Matthew0826/NULunabotics/Mechanical/Chassis/Chassis v4/1602-0032-0008 assembly.STEP

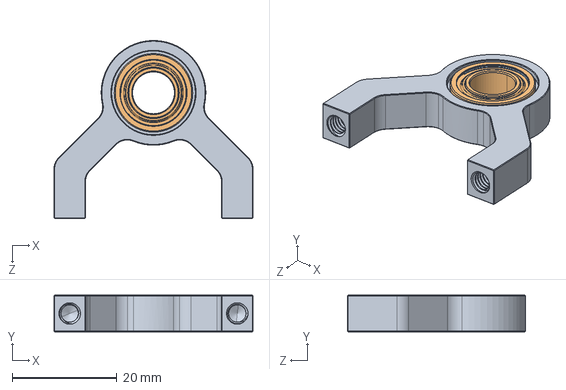
[picture p1: CAD file, 2025-11-15]
Mechanical/Chassis/Chassis v4/1602-0032-0008 assembly.STEP
38.0 x 7.00 x 34.0 mm
