Matthew0826/NULunabotics/Electrical/SparkMiniMount.SLDPRT

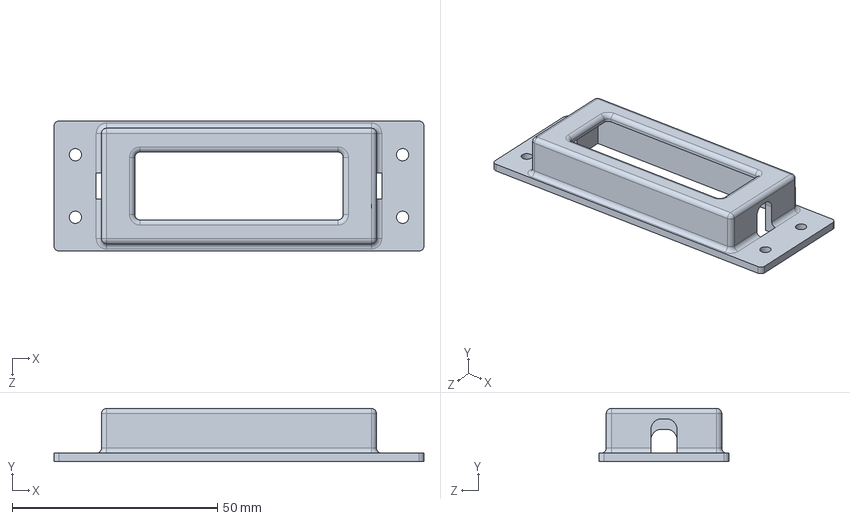
[picture p2: CAD file, 2025-05-19]
Electrical/SparkMiniMount.SLDPRT
90.2 x 13.0 x 31.8 mm
