Matthew0826/NULunabotics/Mechanical/4BarGBOuter.STL

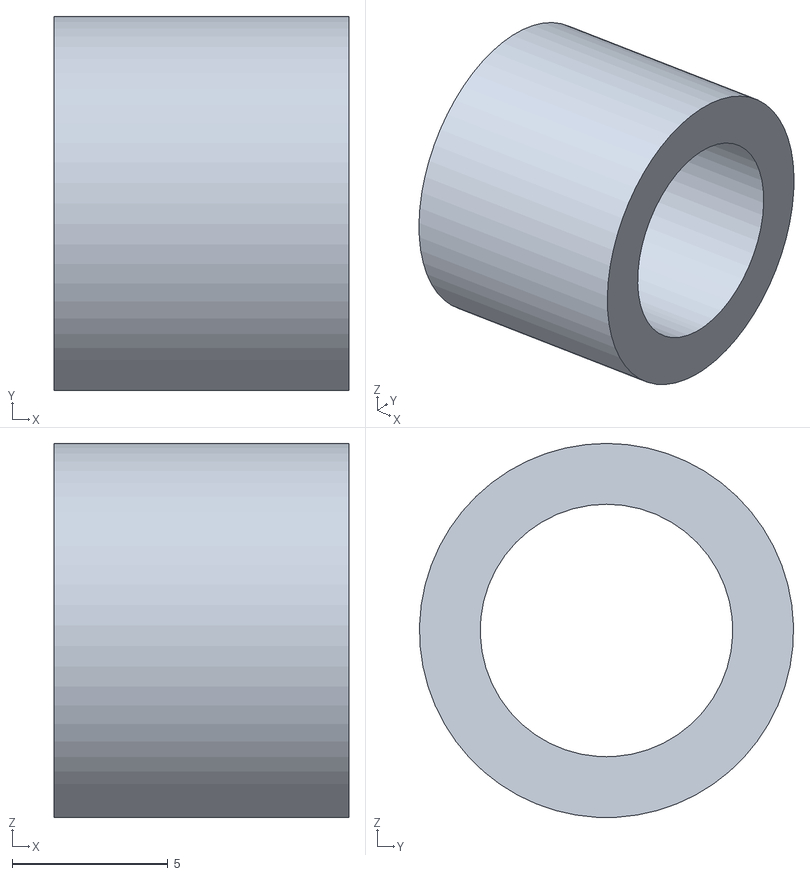
[picture p3: CAD file, 2025-11-15]
Mechanical/4BarGBOuter.STL
9.46 x 12.0 x 12.0
