Matthew0826/NULunabotics/Mechanical/Chassis/Chassis v4/LargeBottomPlate.SLDPRT

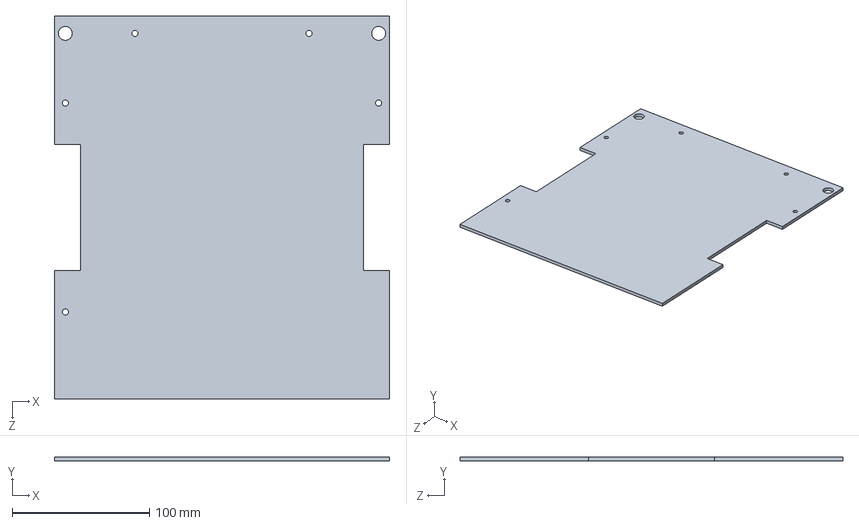
[picture p4: CAD file, 2025-11-15]
Mechanical/Chassis/Chassis v4/LargeBottomPlate.SLDPRT
244.5 x 3.17 x 279.4 mm
