Matthew0826/NULunabotics/Mechanical/Chassis/Maharshi Blocking/Dummy_Wheel_226mm.SLDPRT

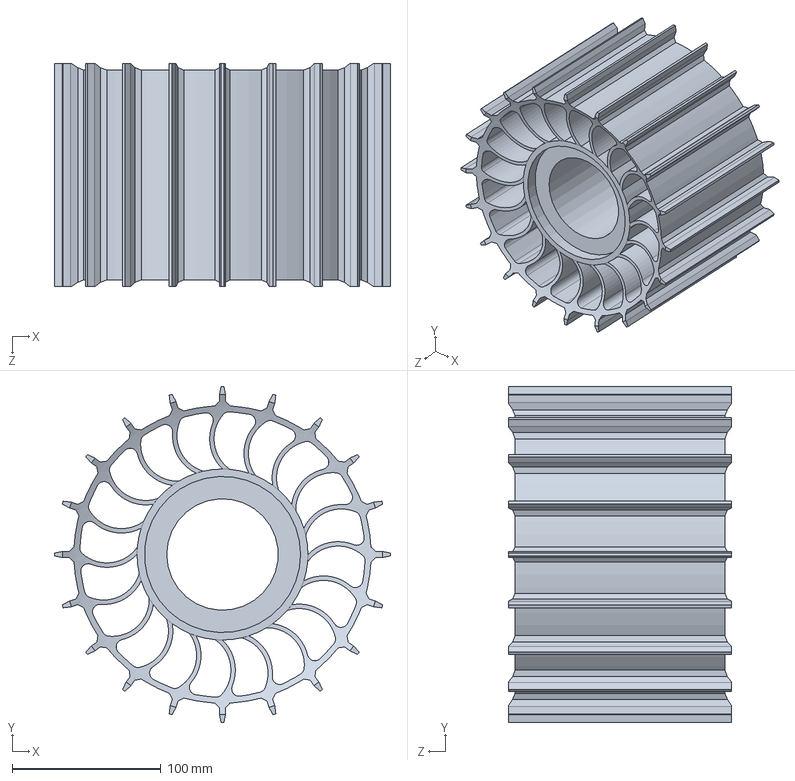
[picture p5: CAD file, 2025-02-20]
Mechanical/Chassis/Maharshi Blocking/Dummy_Wheel_226mm.SLDPRT
226.0 x 226.0 x 150.0 mm
