Matthew0826/NULunabotics/Mechanical/Drivebase/Chassis/Bearing Holder Standard.SLDPRT

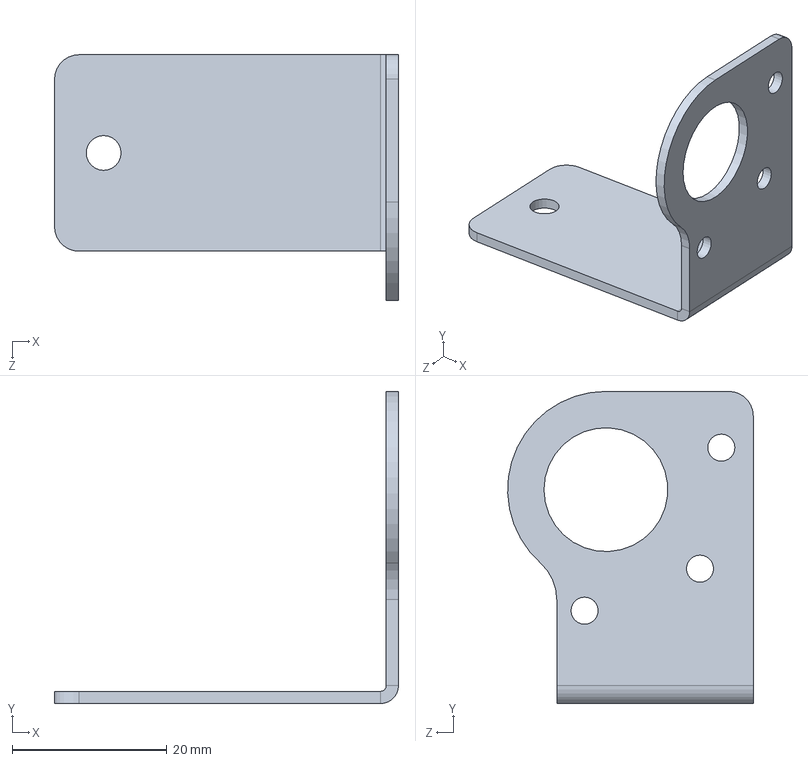
[picture p6: CAD file, 2025-11-15]
Mechanical/Drivebase/Chassis/Bearing Holder Standard.SLDPRT
44.5 x 40.3 x 31.7 mm
