Matthew0826/NULunabotics/Mechanical/Drivebase/Chassis/Frame/Side L-Bar.SLDPRT

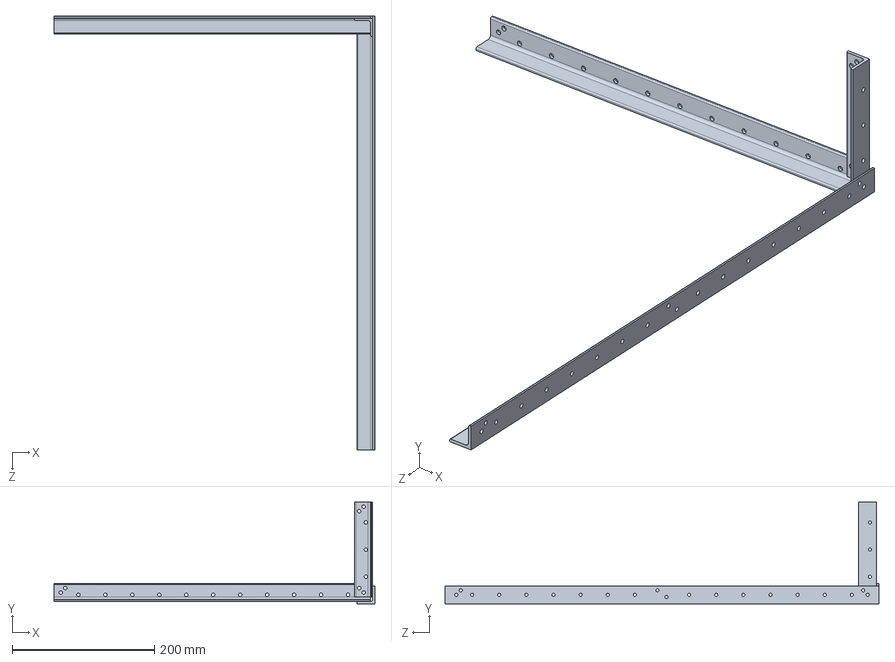
[picture p7: CAD file, 2025-11-15]
Mechanical/Drivebase/Chassis/Frame/Side L-Bar.SLDPRT
450.8 x 142.9 x 609.6 mm
