Matthew0826/NULunabotics/Mechanical/Excavation/Conveyer/Excavator Spacer 1.1in.STL

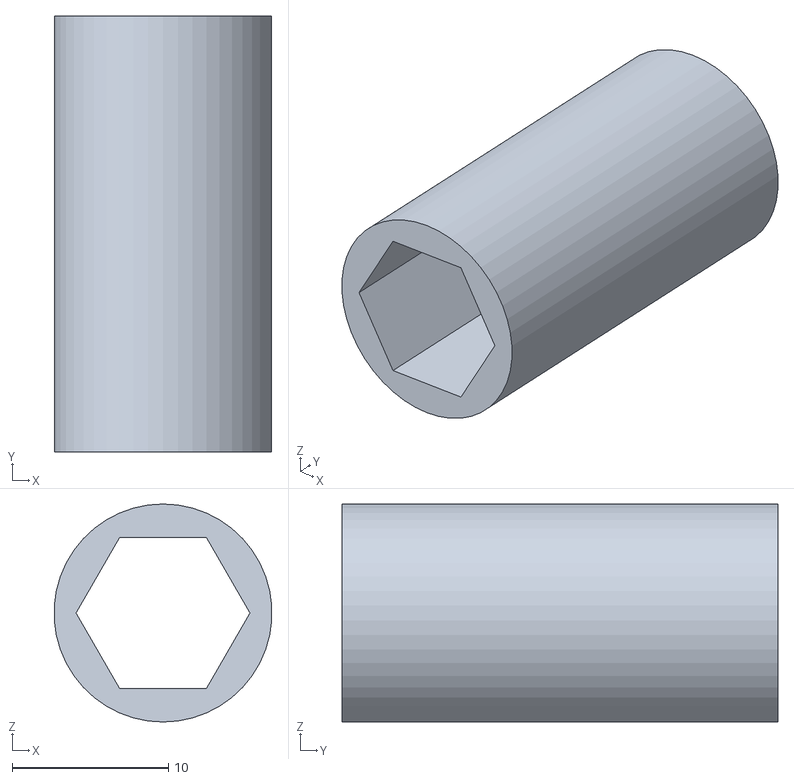
[picture p8: CAD file, 2025-03-28]
Mechanical/Excavation/Conveyer/Excavator Spacer 1.1in.STL
13.9 x 27.9 x 14.0
