Matthew0826/NULunabotics/Mechanical/Excavation/Dump/DumpCut.DXF

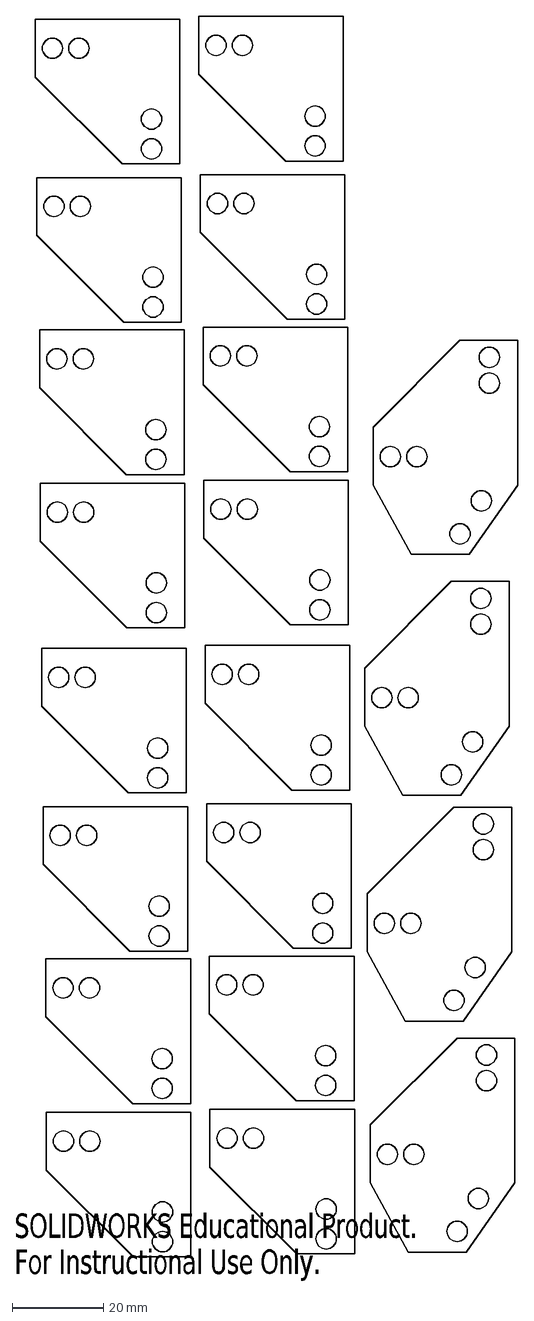
[picture p9: CAD file, 2025-11-15]
Mechanical/Excavation/Dump/DumpCut.DXF
SOLIDWORKS Educational Product.
For Instructional Use Only.
