Matthew0826/NULunabotics/Mechanical/Excavation/Excavator/Waterjet Reference_imported_DWG.dxf

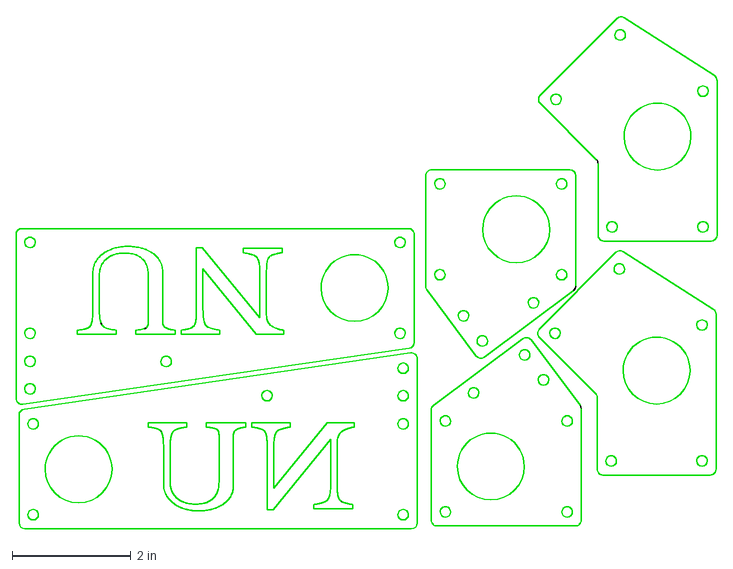
[picture p10: CAD file, 2025-11-15]
Mechanical/Excavation/Excavator/Waterjet Reference_imported_DWG.dxf
11.8 x 8.62 in
