Matthew0826/NULunabotics/Mechanical/Excavation/hexHoldPlate.SLDPRT

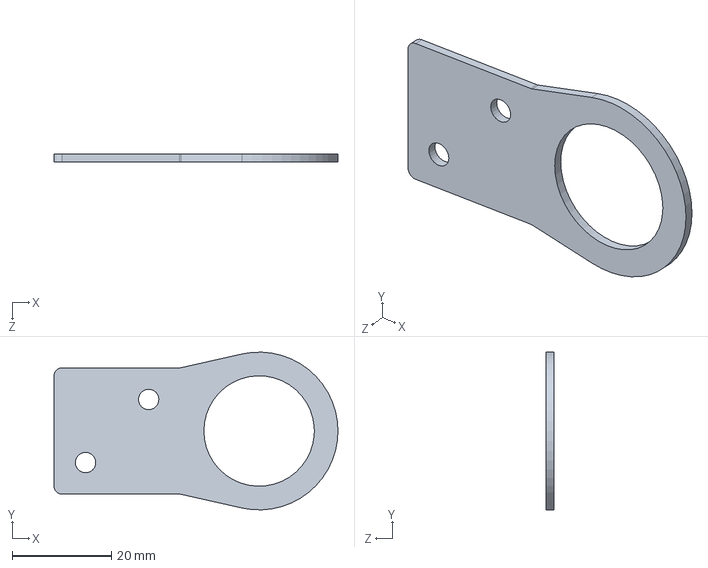
[picture p11: CAD file, 2025-11-15]
Mechanical/Excavation/hexHoldPlate.SLDPRT
57.2 x 31.7 x 1.59 mm
