Matthew0826/NULunabotics/Mechanical/Excavation/Scoops/Excavator Spacer 2.22 in.SLDPRT

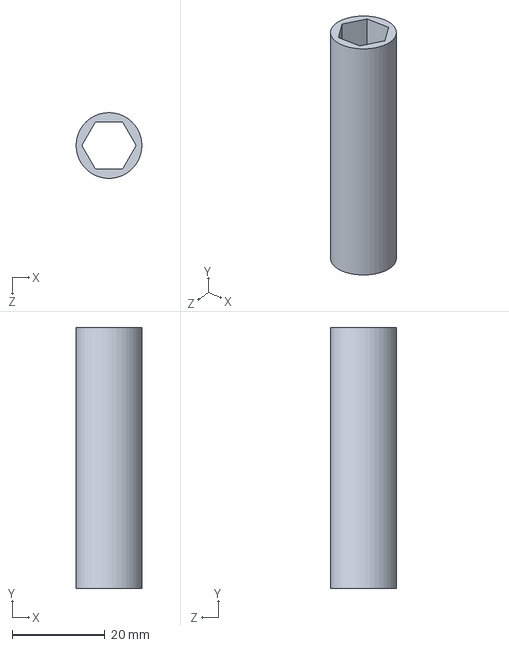
[picture p12: CAD file, 2025-03-31]
Mechanical/Excavation/Scoops/Excavator Spacer 2.22 in.SLDPRT
14.2 x 56.4 x 14.2 mm
