Matthew0826/NULunabotics/Mechanical/Experimental/Swerve Modules/Chassis Structure/Fixed Components/Gearbox Casing/Motor Mounting Plate.SLDPRT

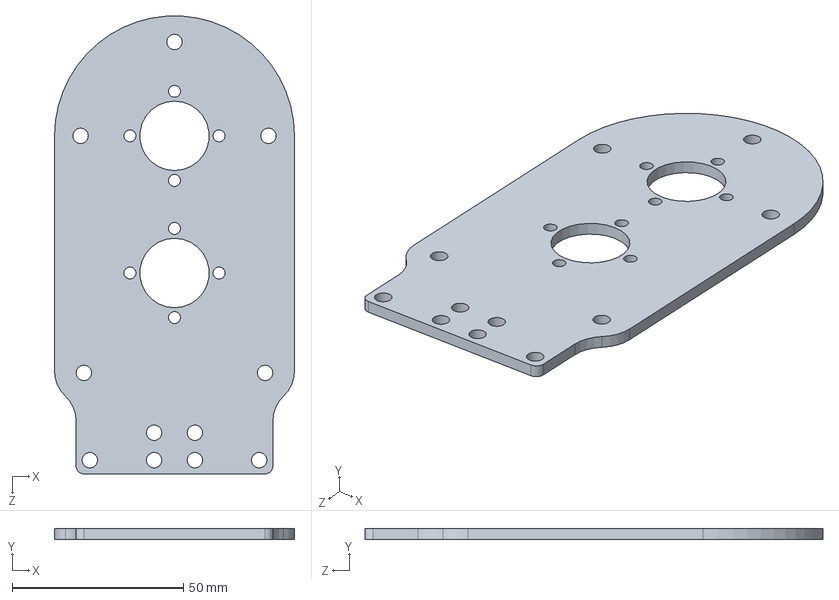
[picture p13: CAD file, 2025-11-15]
Mechanical/Experimental/Swerve Modules/Chassis Structure/Fixed Components/Gearbox Casing/Motor Mounting Plate.SLDPRT
70.0 x 3.18 x 133.5 mm
