Matthew0826/NULunabotics/Mechanical/Experimental/Swerve Modules/Chassis Structure/Fixed Components/Tube Mount/Tube Clamp Plate.SLDPRT

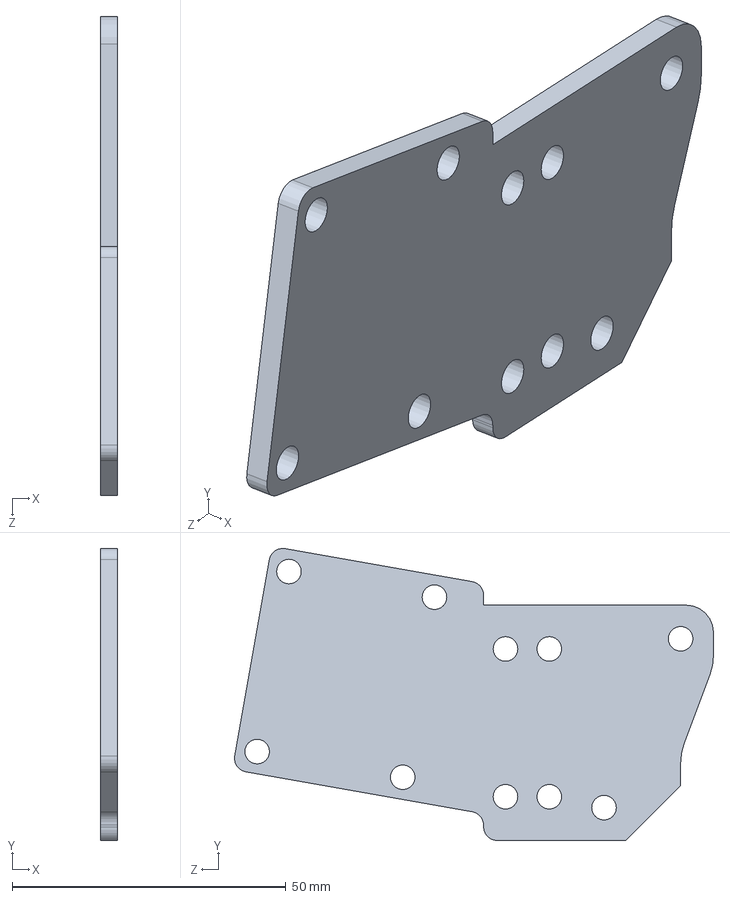
[picture p14: CAD file, 2025-11-15]
Mechanical/Experimental/Swerve Modules/Chassis Structure/Fixed Components/Tube Mount/Tube Clamp Plate.SLDPRT
3.17 x 53.4 x 87.5 mm
