Matthew0826/NULunabotics/Mechanical/Experimental/Swerve Modules/Chassis Structure/Top Spacer.SLDPRT

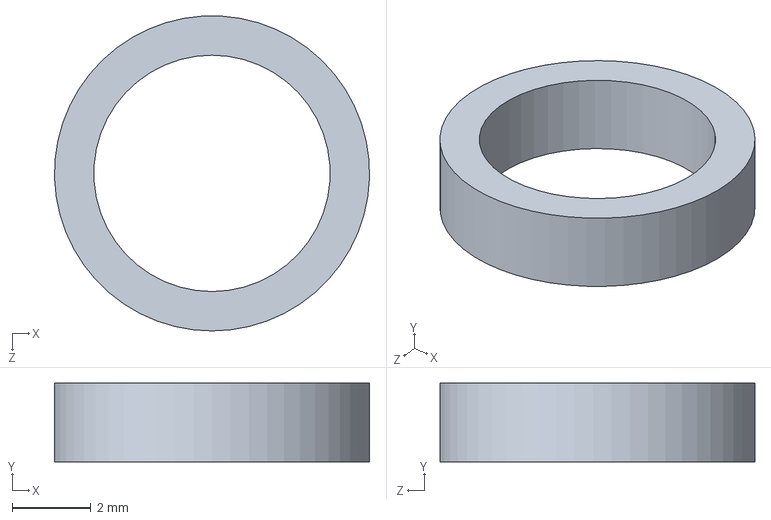
[picture p15: CAD file, 2025-11-15]
Mechanical/Experimental/Swerve Modules/Chassis Structure/Top Spacer.SLDPRT
8.00 x 2.00 x 7.99 mm
