Matthew0826/NULunabotics/Mechanical/Experimental/Swerve Modules/LidarMount.SLDPRT

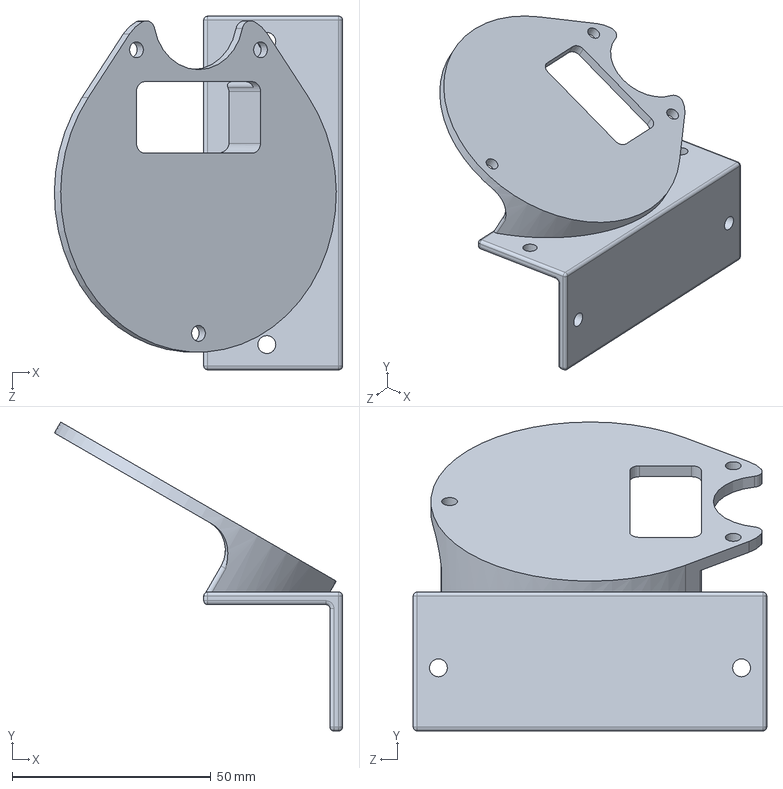
[picture p16: CAD file, 2025-11-15]
Mechanical/Experimental/Swerve Modules/LidarMount.SLDPRT
72.5 x 77.7 x 88.9 mm
