Matthew0826/NULunabotics/Mechanical/Experimental/Swerve Modules/Wheel Structure/Fixed Components/Wheel Tube.SLDPRT

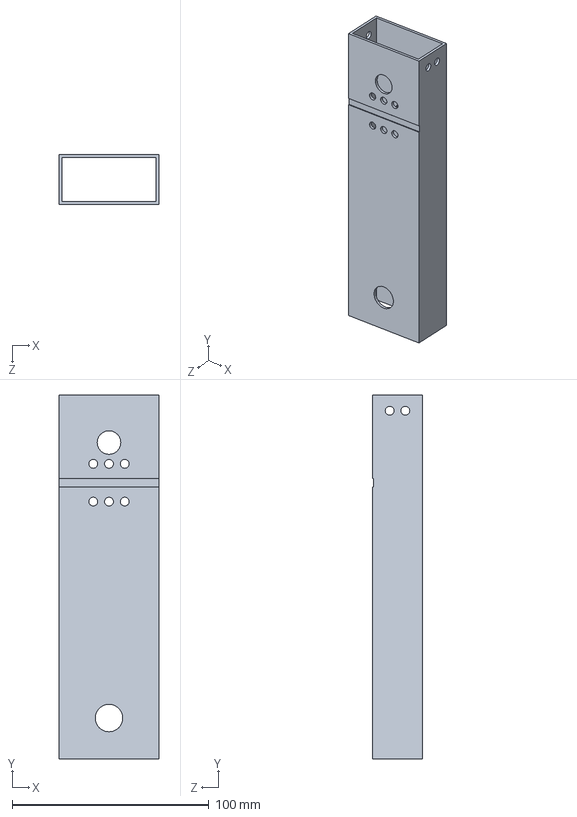
[picture p17: CAD file, 2025-11-15]
Mechanical/Experimental/Swerve Modules/Wheel Structure/Fixed Components/Wheel Tube.SLDPRT
50.8 x 185.0 x 25.4 mm
