Matthew0826/NULunabotics/Mechanical/Experimental/Swerve Modules/Wheel Structure/Grouser Wheel Standin.SLDPRT

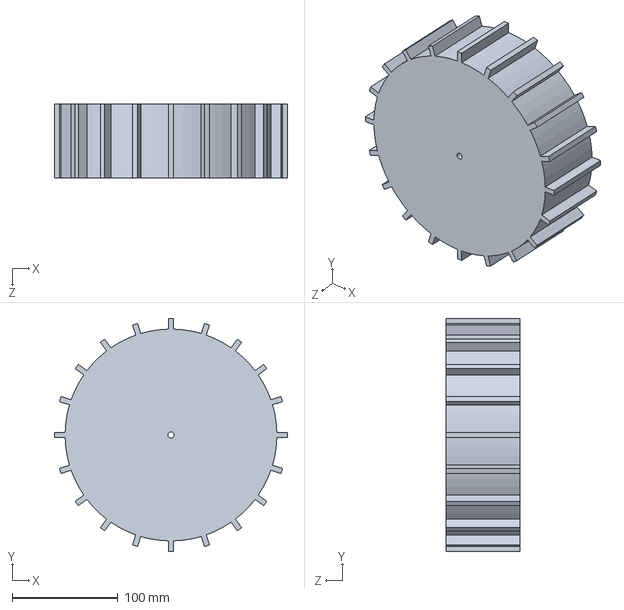
[picture p18: CAD file, 2025-11-15]
Mechanical/Experimental/Swerve Modules/Wheel Structure/Grouser Wheel Standin.SLDPRT
220.0 x 220.0 x 70.0 mm
