Matthew0826/NULunabotics/Mechanical/Generic Parts/Motor.SLDPRT

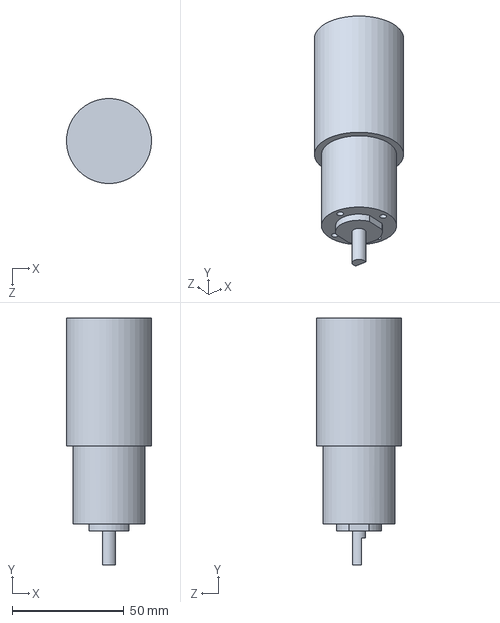
[picture p19: CAD file, 2025-11-15]
Mechanical/Generic Parts/Motor.SLDPRT
38.0 x 110.3 x 38.0 mm
