Matthew0826/NULunabotics/Mechanical/Lunabotics2025_Chassis_Design/Chassis_2/1x1inch_60mmBeam.SLDPRT

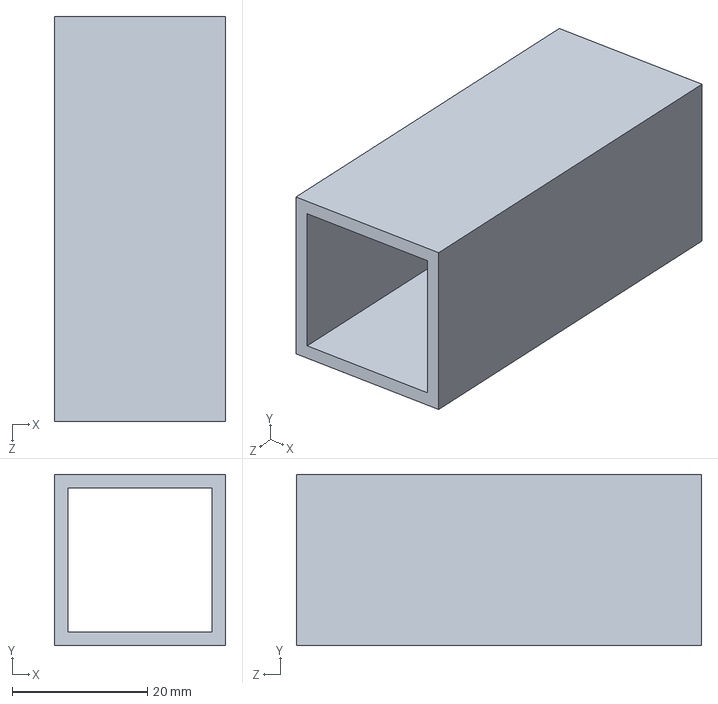
[picture p20: CAD file, 2025-03-20]
Mechanical/Lunabotics2025_Chassis_Design/Chassis_2/1x1inch_60mmBeam.SLDPRT
25.4 x 25.4 x 60.0 mm
