Matthew0826/NULunabotics/Mechanical/Lunabotics2025_Chassis_Design/Conveyer/Rib_3.SLDPRT

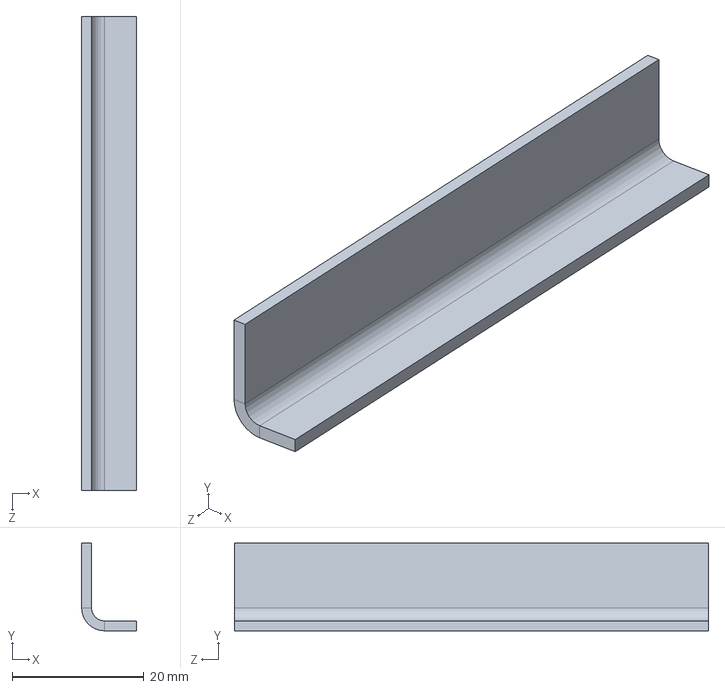
[picture p21: CAD file, 2025-02-18]
Mechanical/Lunabotics2025_Chassis_Design/Conveyer/Rib_3.SLDPRT
8.32 x 13.3 x 72.0 mm
