Matthew0826/NULunabotics/Mechanical/Lunabotics2025_Chassis_Design/Dummy_Arm-2.SLDPRT

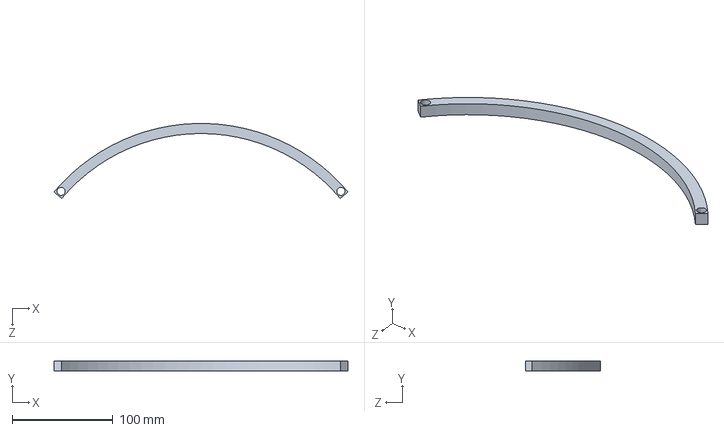
[picture p22: CAD file, 2025-02-18]
Mechanical/Lunabotics2025_Chassis_Design/Dummy_Arm-2.SLDPRT
291.1 x 10.0 x 74.2 mm
