Matthew0826/NULunabotics/Mechanical/Rocker/Bearing Holder.SLDPRT

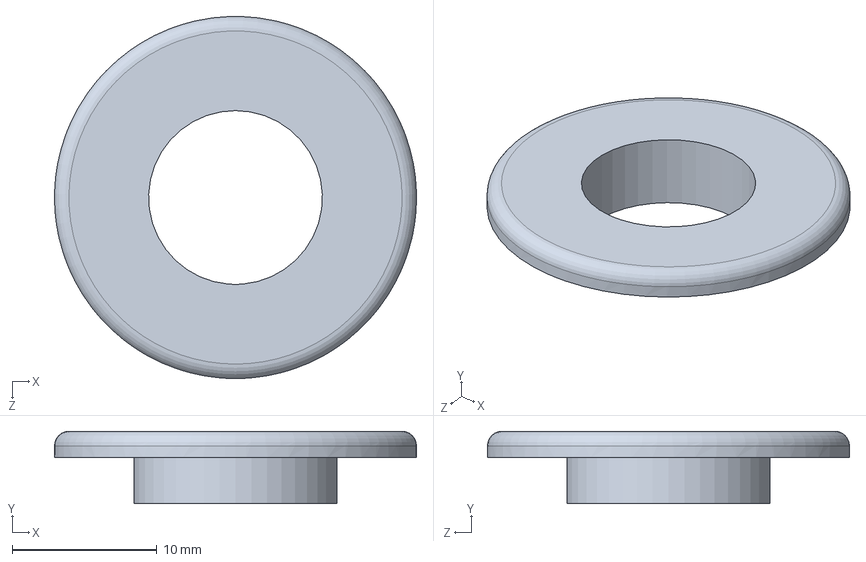
[picture p23: CAD file, 2025-11-15]
Mechanical/Rocker/Bearing Holder.SLDPRT
25.0 x 5.00 x 25.0 mm
