Matthew0826/NULunabotics/Mechanical/Sensors/RBP_Case.SLDPRT

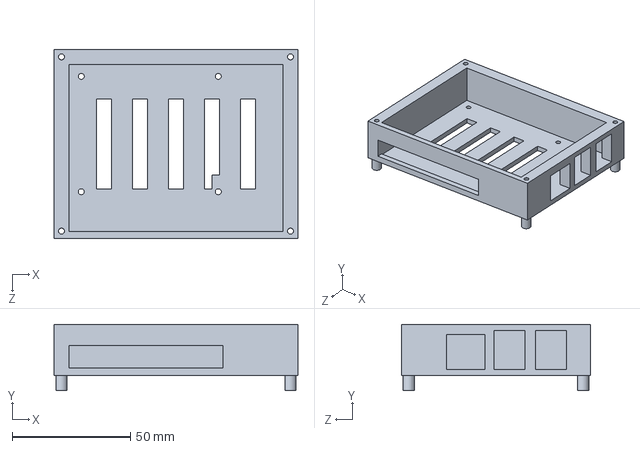
[picture p24: CAD file, 2025-03-28]
Mechanical/Sensors/RBP_Case.SLDPRT
103.1 x 27.9 x 80.0 mm
