Matthew0826/NULunabotics/Mechanical/Wheel/Wheel_Spacer.SLDPRT

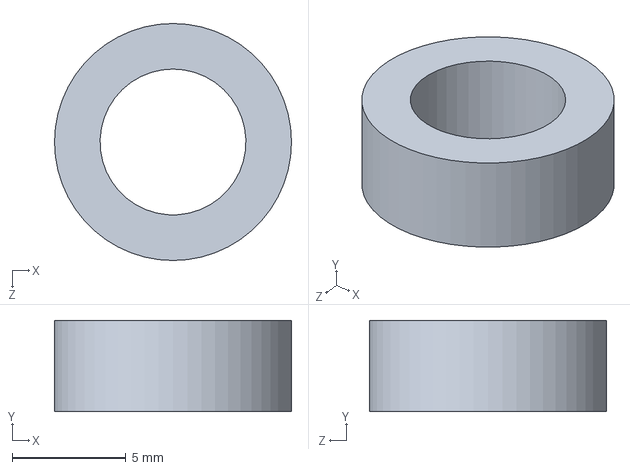
[picture p25: CAD file, 2025-11-15]
Mechanical/Wheel/Wheel_Spacer.SLDPRT
10.4 x 4.00 x 10.4 mm
