Matthew0826/NULunabotics/Software/ROS2/src/website/public/models/lunabot_wheel.obj

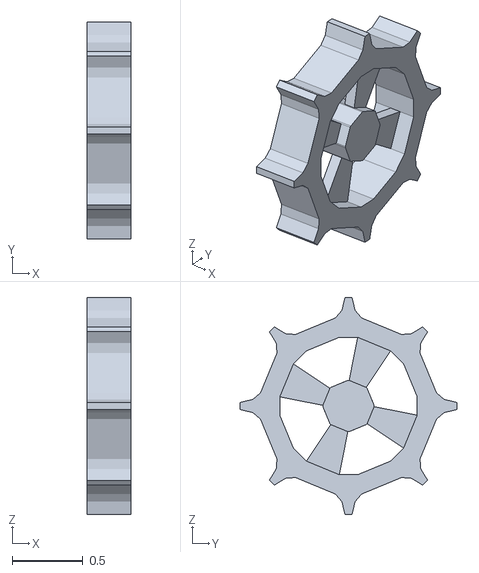
[picture p26: CAD file, 2025-11-15]
Software/ROS2/src/website/public/models/lunabot_wheel.obj
0.309 x 1.54 x 1.54
