Matthew0826/NULunabotics/Software/ROS2/src/website/public/models/theia/wheelRB.obj

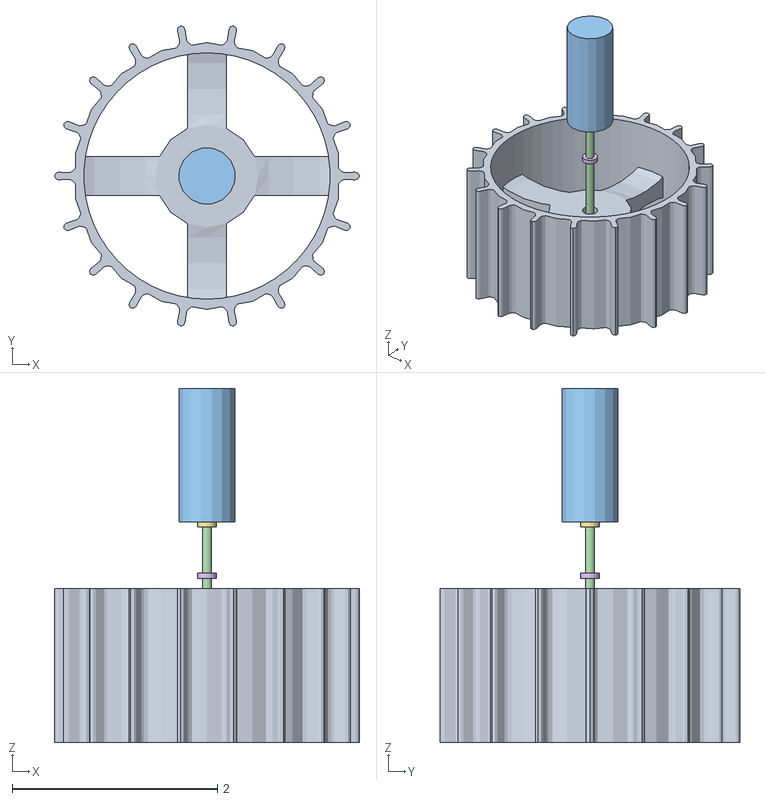
[picture p27: CAD file, 2025-11-15]
Software/ROS2/src/website/public/models/theia/wheelRB.obj
2.97 x 2.93 x 3.45
Rim.004
Bolt.004
Shaft.003
Baring.005
Baring.006
Baring.007
