Matthew0826/NULunabotics/Mechanical/Chassis/Maharshi Blocking/Dummy_Arm-1.SLDPRT

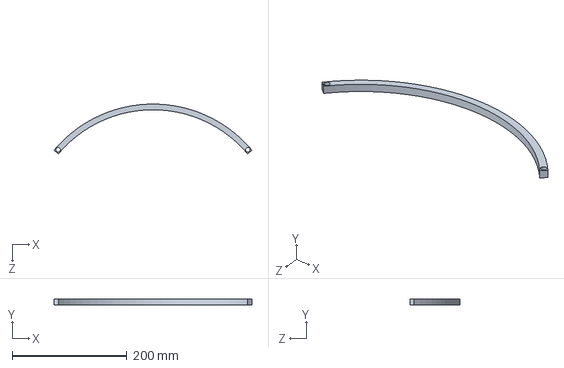
[picture p28: CAD file, 2025-02-20]
Mechanical/Chassis/Maharshi Blocking/Dummy_Arm-1.SLDPRT
344.7 x 10.0 x 86.7 mm
