Matthew0826/NULunabotics/Mechanical/Chassis/Sheet Metal Chassis/Chassis_Rib.SLDPRT

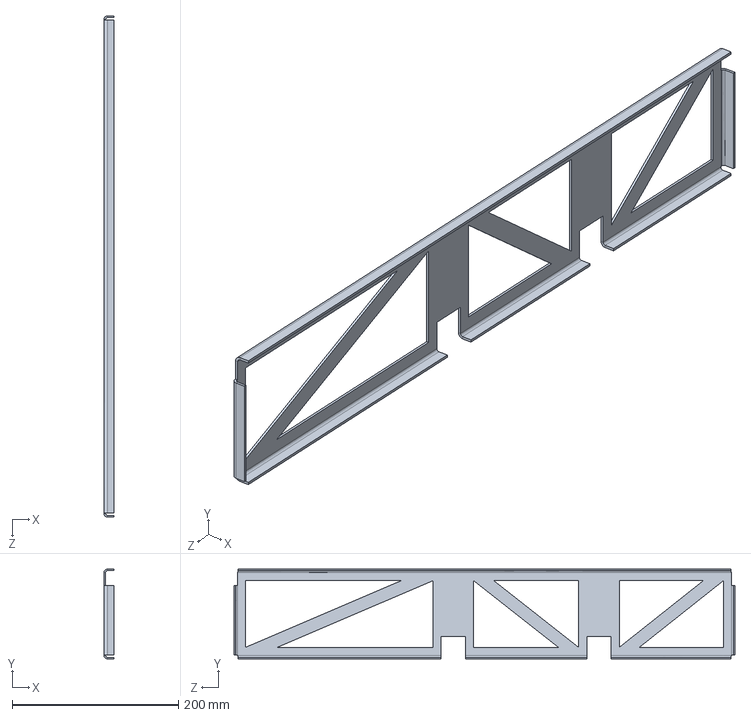
[picture p29: CAD file, 2025-02-20]
Mechanical/Chassis/Sheet Metal Chassis/Chassis_Rib.SLDPRT
12.0 x 108.0 x 602.0 mm
