Matthew0826/NULunabotics/Mechanical/Excavation/Conveyer/Side_Frame.SLDPRT

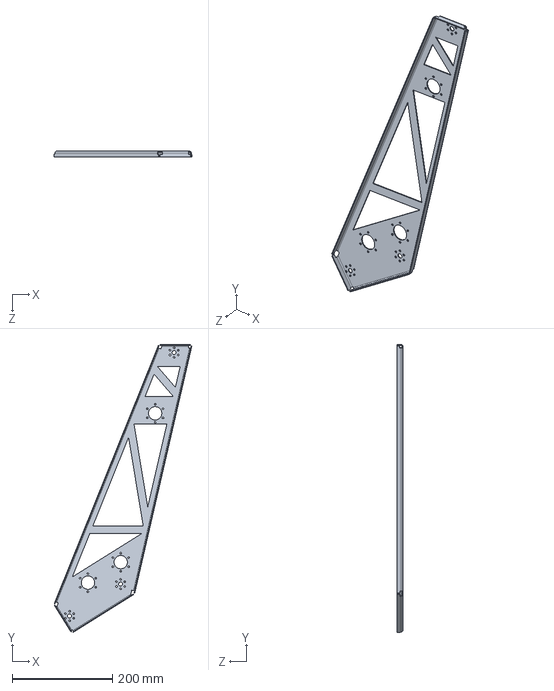
[picture p30: CAD file, 2025-02-20]
Mechanical/Excavation/Conveyer/Side_Frame.SLDPRT
274.5 x 574.5 x 11.3 mm
