Matthew0826/NULunabotics/Mechanical/Excavation/Dump/Spacer.SLDPRT

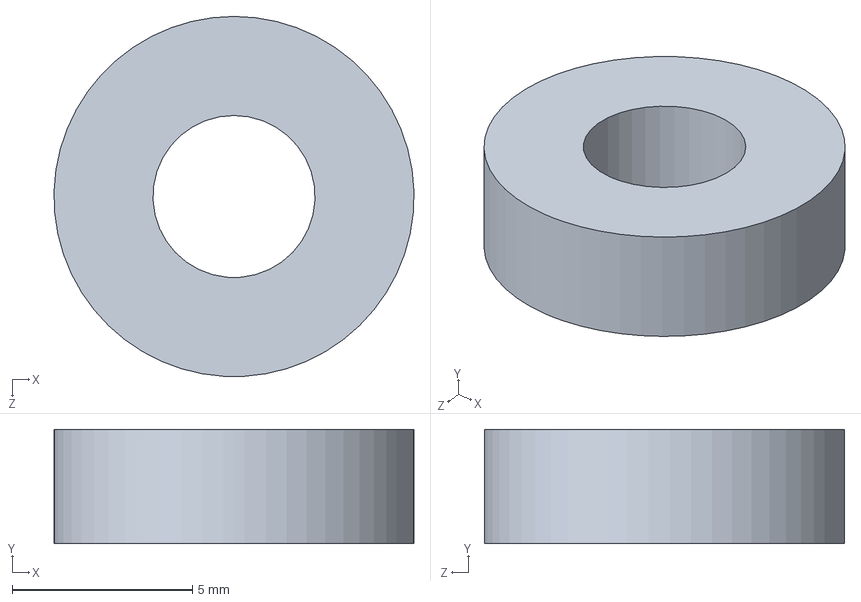
[picture p31: CAD file, 2025-11-15]
Mechanical/Excavation/Dump/Spacer.SLDPRT
10.00 x 3.17 x 10.0 mm
