Matthew0826/NULunabotics/Mechanical/Excavation/Excavator/Motor Toe Gusset.SLDPRT

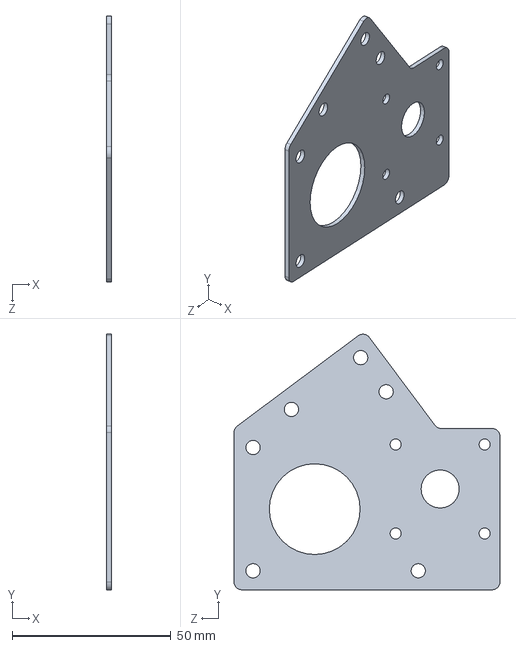
[picture p32: CAD file, 2025-11-15]
Mechanical/Excavation/Excavator/Motor Toe Gusset.SLDPRT
1.59 x 80.5 x 83.7 mm
