Matthew0826/NULunabotics/Mechanical/Excavation/MountHolderMirror.STL

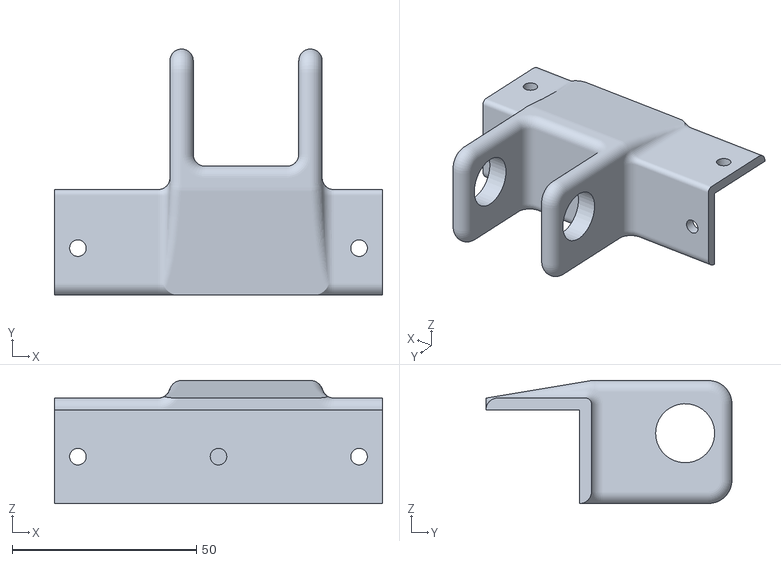
[picture p33: CAD file, 2025-11-15]
Mechanical/Excavation/MountHolderMirror.STL
88.9 x 66.7 x 33.3
