Matthew0826/NULunabotics/Mechanical/Experimental/Swerve Modules/Chassis Structure/12mm Tube 40mm length.SLDPRT

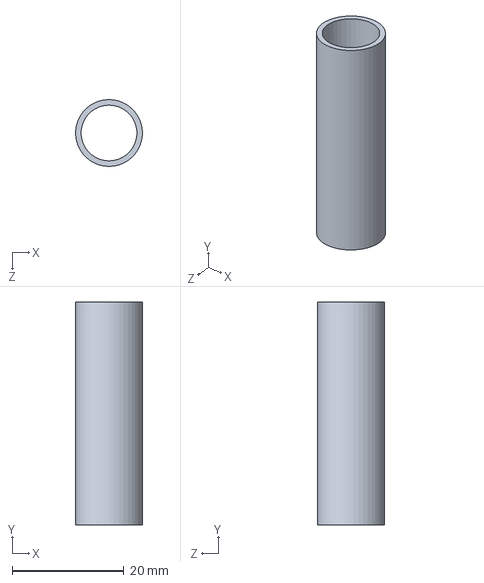
[picture p34: CAD file, 2025-11-15]
Mechanical/Experimental/Swerve Modules/Chassis Structure/12mm Tube 40mm length.SLDPRT
12.0 x 40.0 x 12.0 mm
