Matthew0826/NULunabotics/Mechanical/Experimental/Swerve Modules/Chassis Structure/Fixed Components/Modified GoBilda L-Bracket.SLDPRT

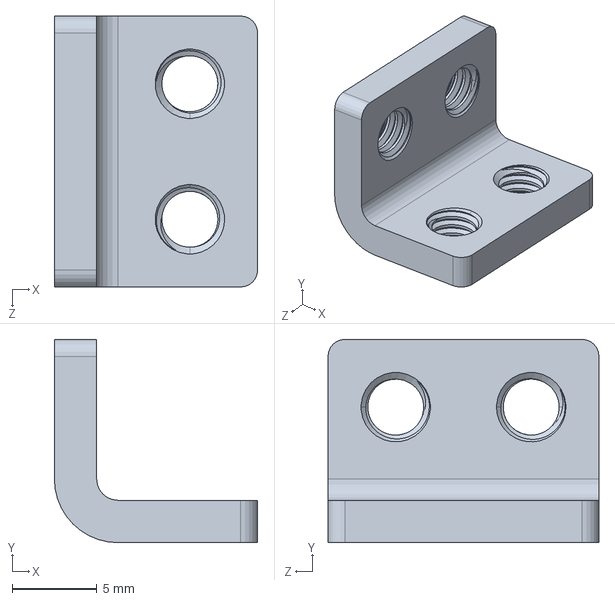
[picture p35: CAD file, 2025-02-19]
Mechanical/Experimental/Swerve Modules/Chassis Structure/Fixed Components/Modified GoBilda L-Bracket.SLDPRT
12.0 x 12.0 x 16.0 mm
