Matthew0826/NULunabotics/Mechanical/Experimental/Swerve Modules/Wheel Structure/Bevel Gear Spacer.SLDPRT

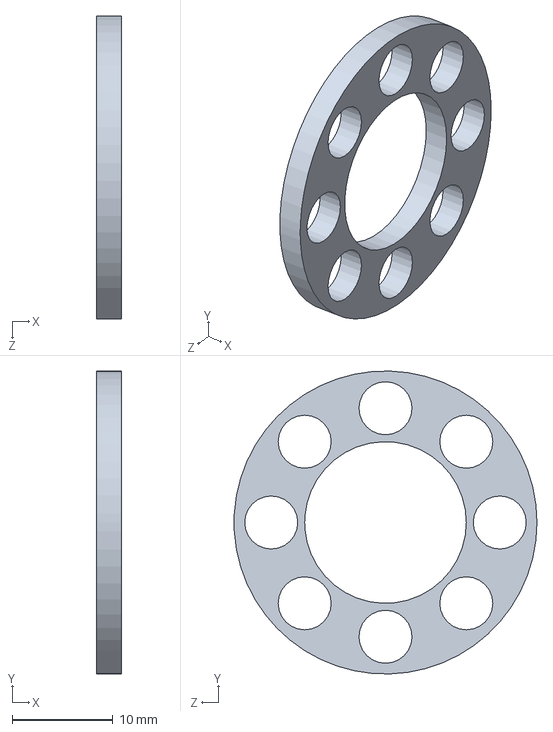
[picture p36: CAD file, 2025-01-24]
Mechanical/Experimental/Swerve Modules/Wheel Structure/Bevel Gear Spacer.SLDPRT
2.50 x 30.0 x 30.0 mm
