Matthew0826/NULunabotics/Mechanical/FaceHolder.SLDPRT

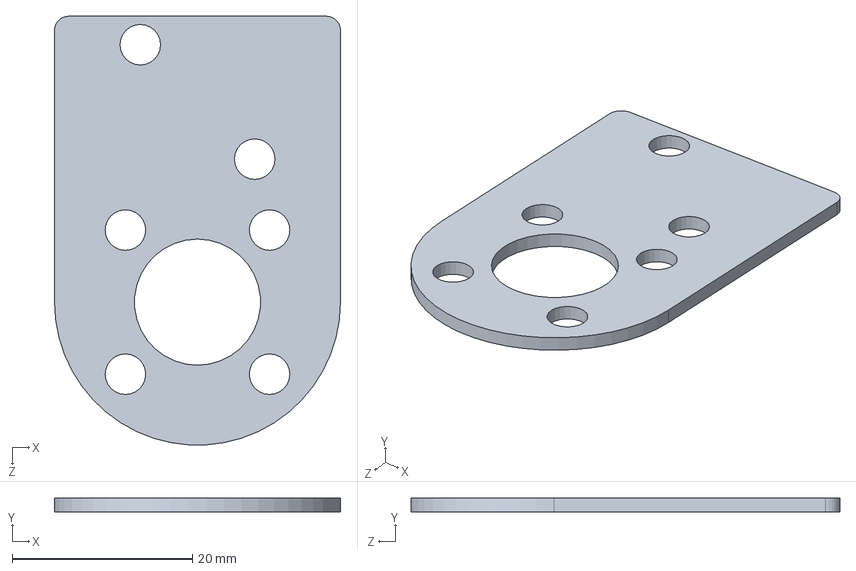
[picture p37: CAD file, 2025-11-15]
Mechanical/FaceHolder.SLDPRT
31.8 x 1.59 x 47.6 mm
