Matthew0826/NULunabotics/Mechanical/Generic Parts/6mm ID 12mm OD bearing.STEP

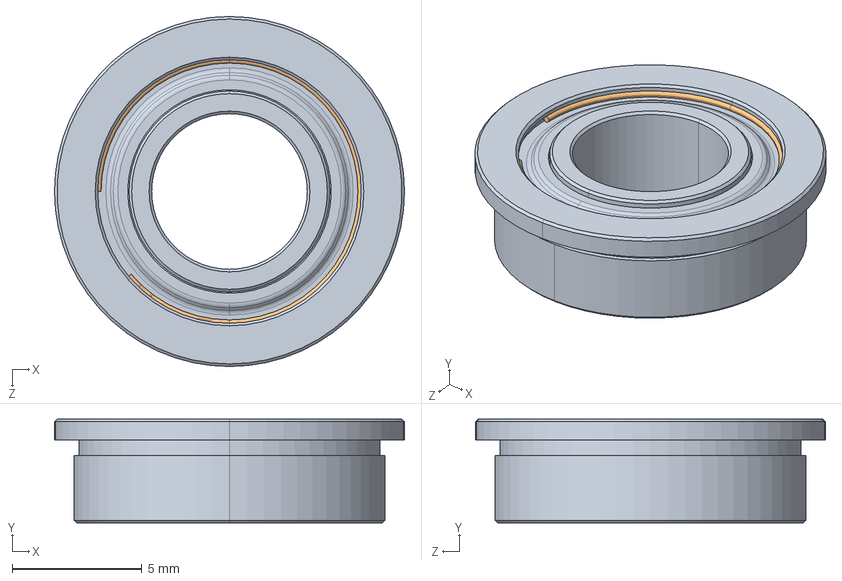
[picture p38: CAD file, 2024-11-07]
Mechanical/Generic Parts/6mm ID 12mm OD bearing.STEP
13.5 x 4.00 x 13.5 mm
