Matthew0826/NULunabotics/Mechanical/Lunabotics2025_Chassis_Design/CAD_Lunbotics 2025/square_Frame_gusset_1.SLDPRT

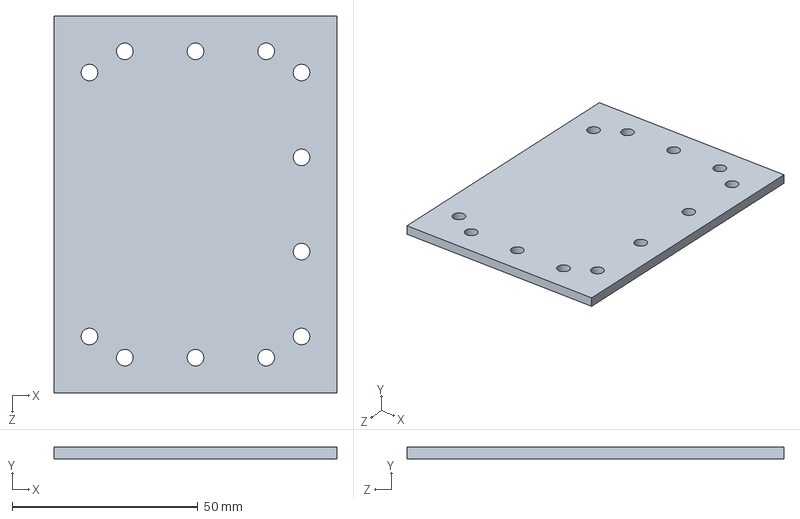
[picture p39: CAD file, 2025-03-20]
Mechanical/Lunabotics2025_Chassis_Design/CAD_Lunbotics 2025/square_Frame_gusset_1.SLDPRT
76.2 x 3.17 x 101.6 mm
