Matthew0826/NULunabotics/Mechanical/Lunabotics2025_Chassis_Design/Chassis_3/9x6inch_side_frame.SLDPRT

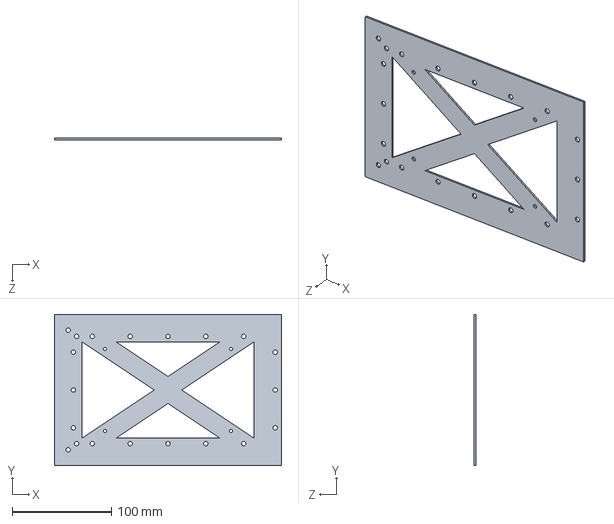
[picture p41: CAD file, 2025-03-20]
Mechanical/Lunabotics2025_Chassis_Design/Chassis_3/9x6inch_side_frame.SLDPRT
228.6 x 152.4 x 1.59 mm
