Matthew0826/NULunabotics/Mechanical/Rocker/DiffBarBearingHolder.SLDPRT

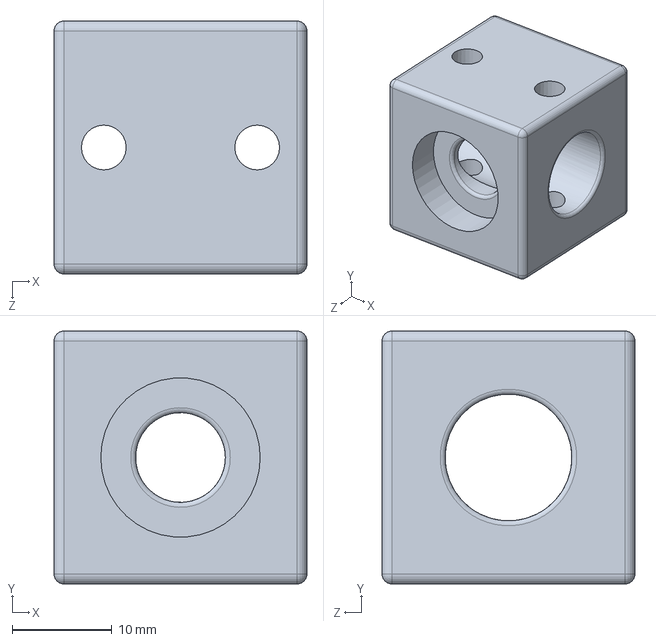
[picture p42: CAD file, 2025-11-15]
Mechanical/Rocker/DiffBarBearingHolder.SLDPRT
25.4 x 25.4 x 25.4 mm
