Matthew0826/NULunabotics/Mechanical/Wheel/hub test.SLDPRT

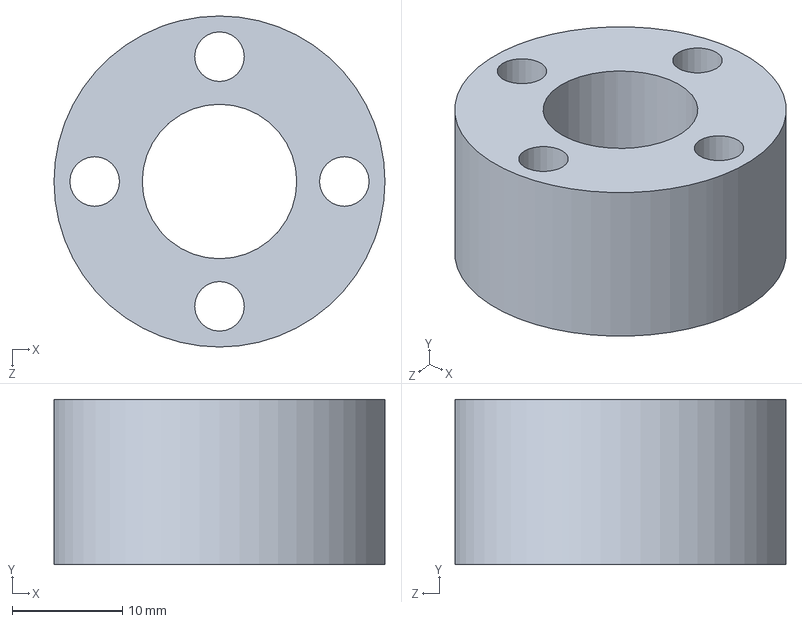
[picture p43: CAD file, 2025-03-14]
Mechanical/Wheel/hub test.SLDPRT
30.0 x 15.0 x 30.0 mm
