Matthew0826/NULunabotics/Software/ROS2/src/website/public/models/lunabot_base.obj

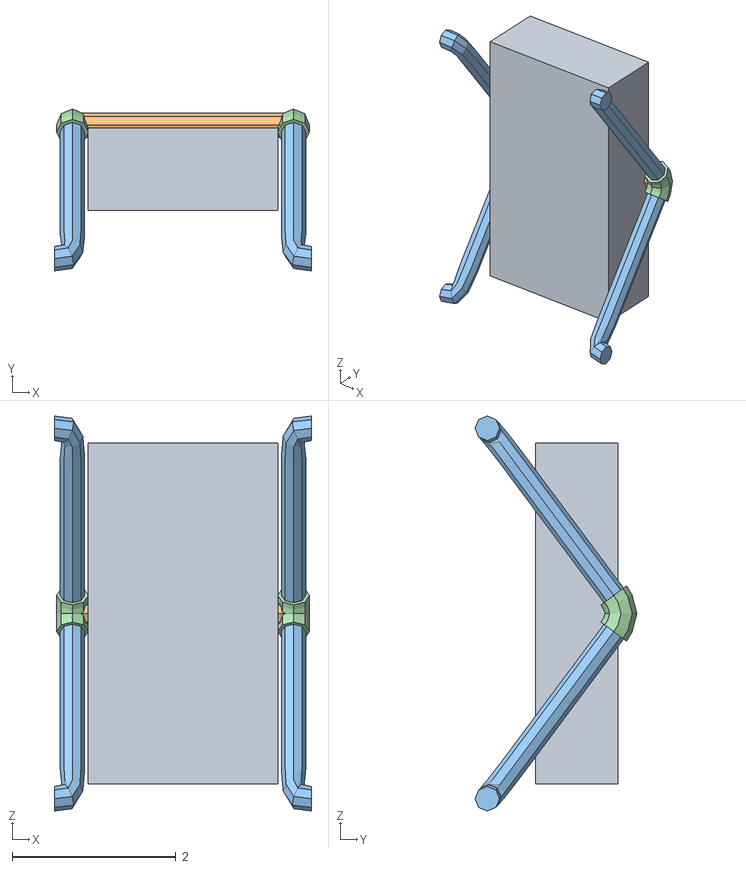
[picture p44: CAD file, 2025-11-15]
Software/ROS2/src/website/public/models/lunabot_base.obj
3.15 x 1.98 x 4.83
