Matthew0826/NULunabotics/Software/ROS2/src/website/public/models/theia/scuffedMotors.obj

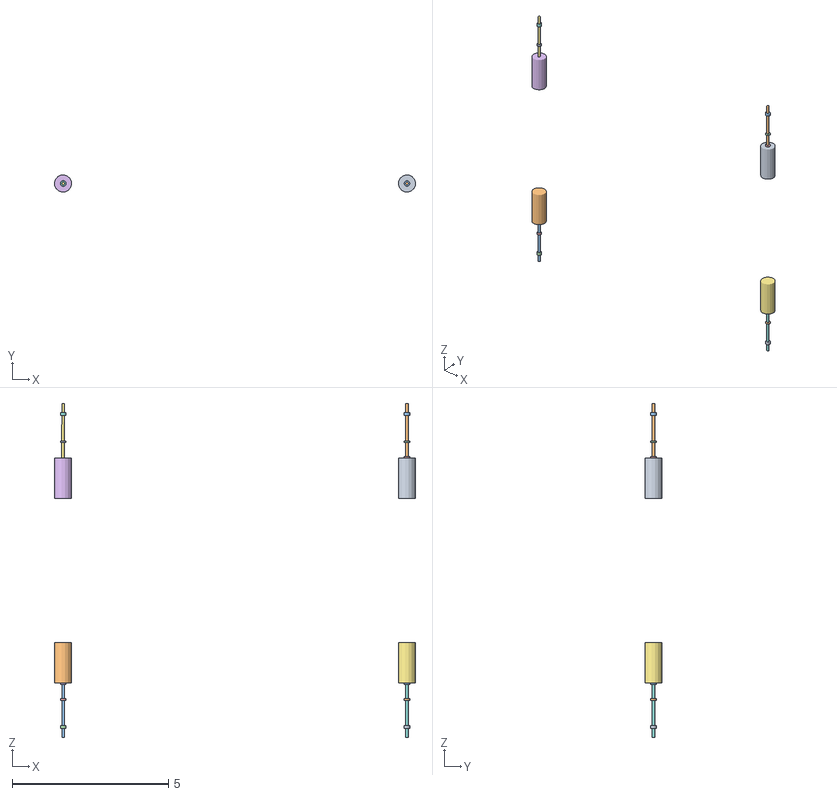
[picture p45: CAD file, 2025-11-15]
Software/ROS2/src/website/public/models/theia/scuffedMotors.obj
11.5 x 0.545 x 10.7
Shaft.012
Baring.001
Baring.003
Baring.004
Shaft.008
Baring.011
Baring.012
Shaft.013
Baring.008
Baring.009
Baring.010
Shaft.003
Baring.005
Baring.006
Baring.007
