Matthew0826/NULunabotics/Mechanical/Chassis/Sheet Metal Chassis/Chassis_Top-Shell.SLDPRT

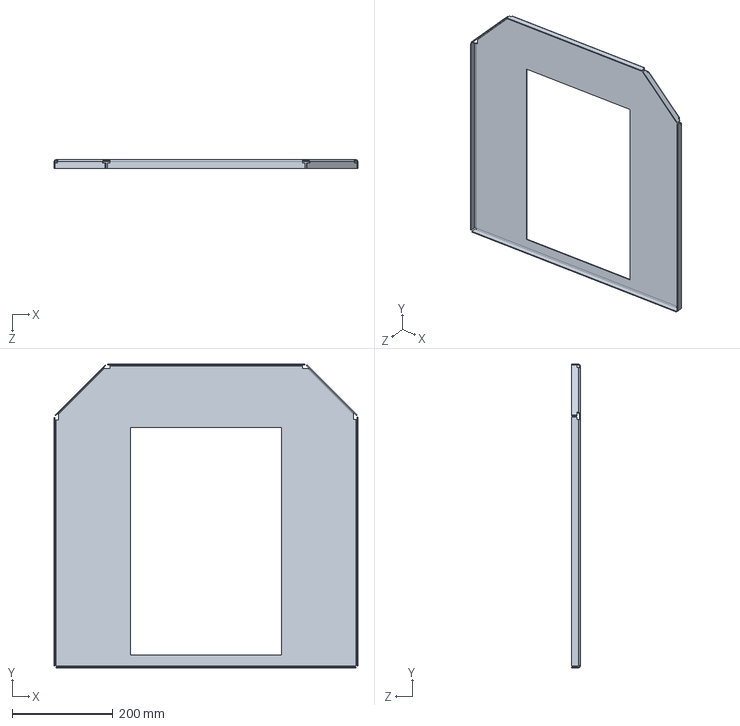
[picture p46: CAD file, 2025-02-20]
Mechanical/Chassis/Sheet Metal Chassis/Chassis_Top-Shell.SLDPRT
602.0 x 602.0 x 17.0 mm
