Matthew0826/NULunabotics/Mechanical/Drivebase/Chassis/Frame/Long Bottom L-Bar.SLDPRT

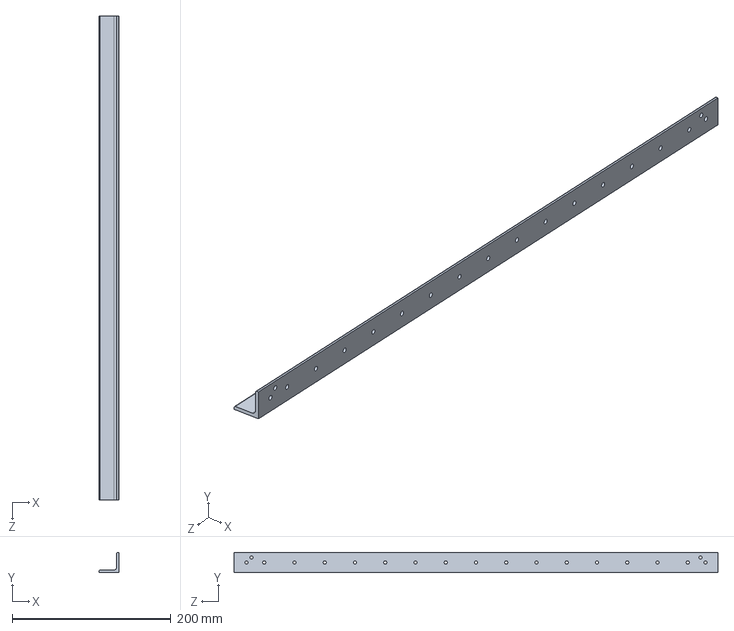
[picture p47: CAD file, 2025-11-15]
Mechanical/Drivebase/Chassis/Frame/Long Bottom L-Bar.SLDPRT
25.4 x 25.4 x 609.6 mm
