Matthew0826/NULunabotics/Mechanical/Excavation/8mm HoldPlate.SLDPRT

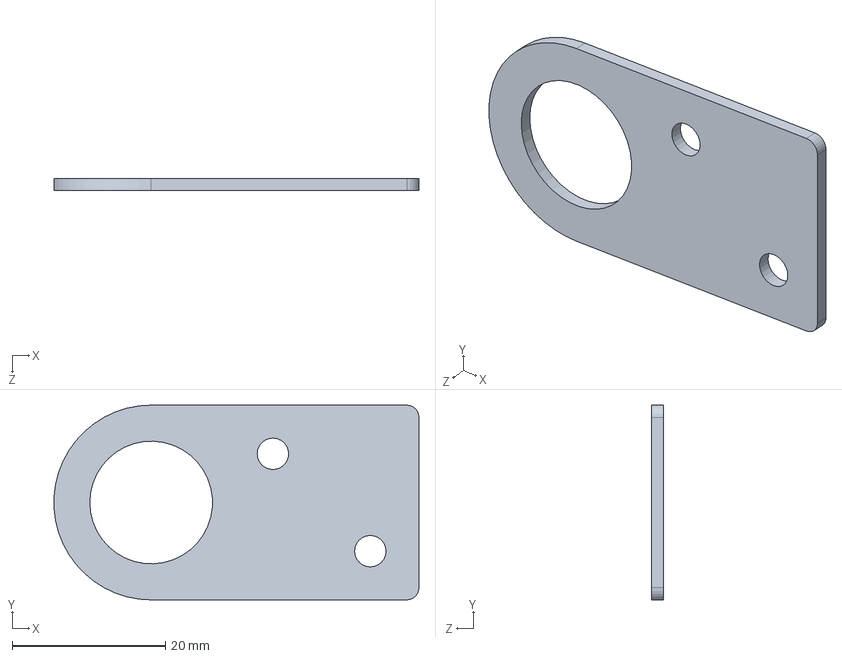
[picture p48: CAD file, 2025-11-15]
Mechanical/Excavation/8mm HoldPlate.SLDPRT
47.6 x 25.4 x 1.59 mm
