Matthew0826/NULunabotics/Mechanical/Excavation/Conveyer/Rib_1.SLDPRT

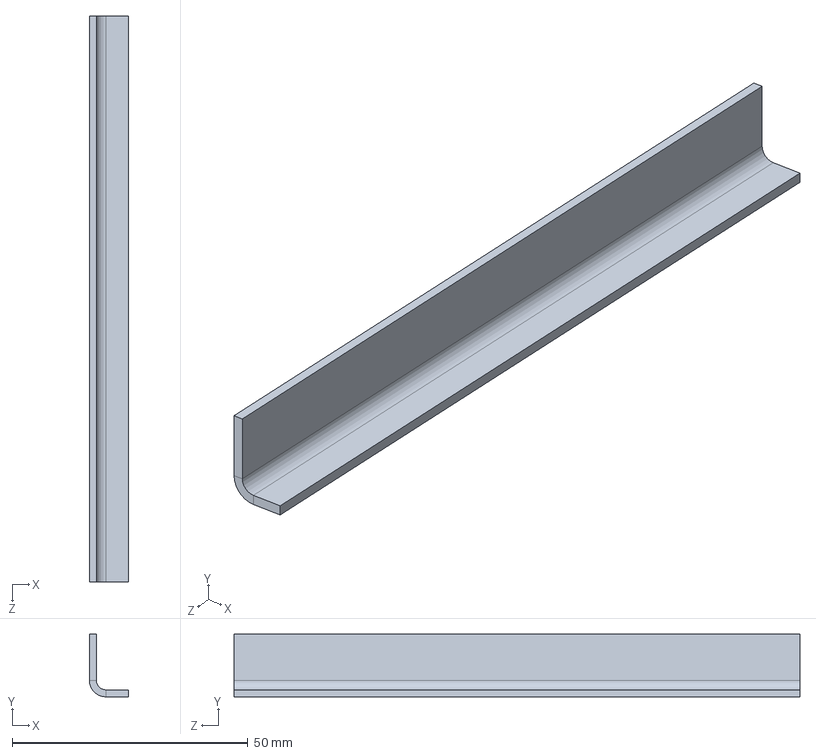
[picture p49: CAD file, 2025-02-20]
Mechanical/Excavation/Conveyer/Rib_1.SLDPRT
8.32 x 13.3 x 120.0 mm
