Matthew0826/NULunabotics/Mechanical/Excavation/Excavator/Knee Gusset 16.DXF

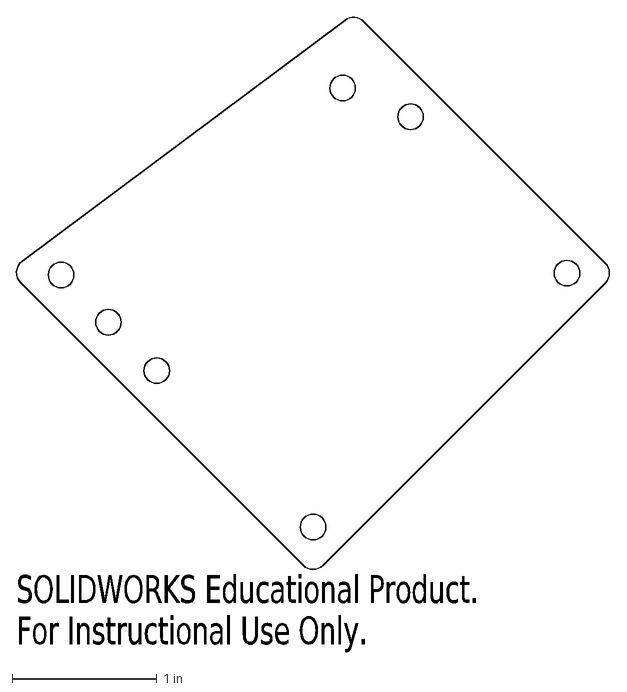
[picture p50: CAD file, 2025-11-15]
Mechanical/Excavation/Excavator/Knee Gusset 16.DXF
SOLIDWORKS Educational Product.
For Instructional Use Only.
