Matthew0826/NULunabotics/Mechanical/Excavation/Scoops/Lunabotics Scoop.SLDPRT

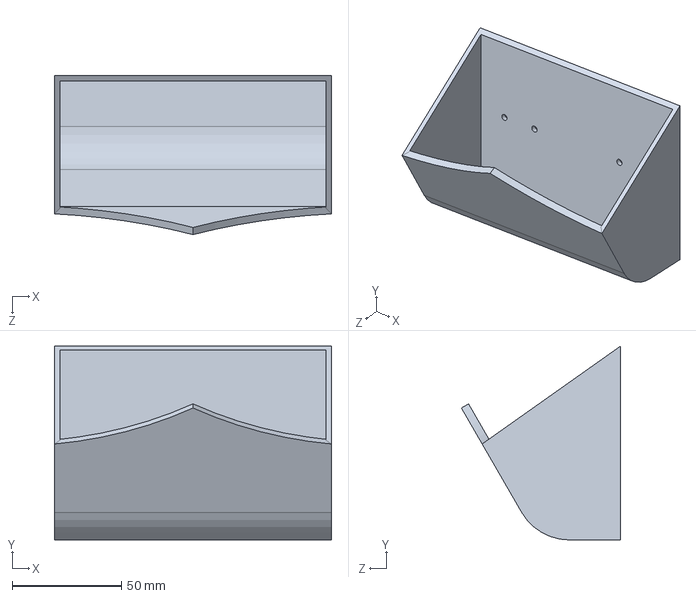
[picture p51: CAD file, 2025-03-21]
Mechanical/Excavation/Scoops/Lunabotics Scoop.SLDPRT
127.0 x 88.9 x 73.0 mm
