Matthew0826/NULunabotics/Mechanical/Experimental/Swerve Modules/Chassis Structure/Fixed Components/Tube Mount/Tube Clamp Right.SLDPRT

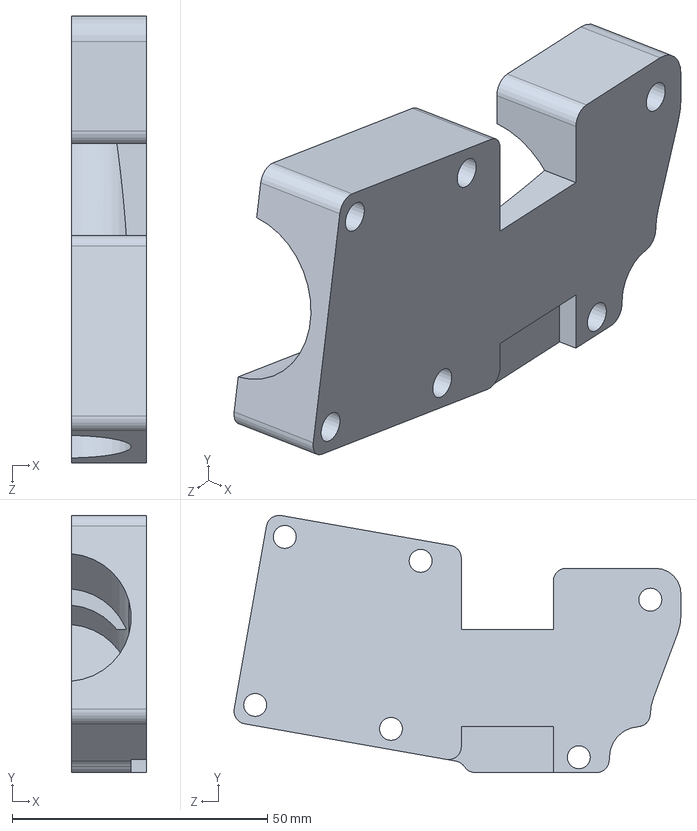
[picture p52: CAD file, 2025-11-15]
Mechanical/Experimental/Swerve Modules/Chassis Structure/Fixed Components/Tube Mount/Tube Clamp Right.SLDPRT
14.7 x 50.4 x 87.5 mm
