Matthew0826/NULunabotics/Mechanical/Experimental/Swerve Modules/UWBMount.SLDPRT

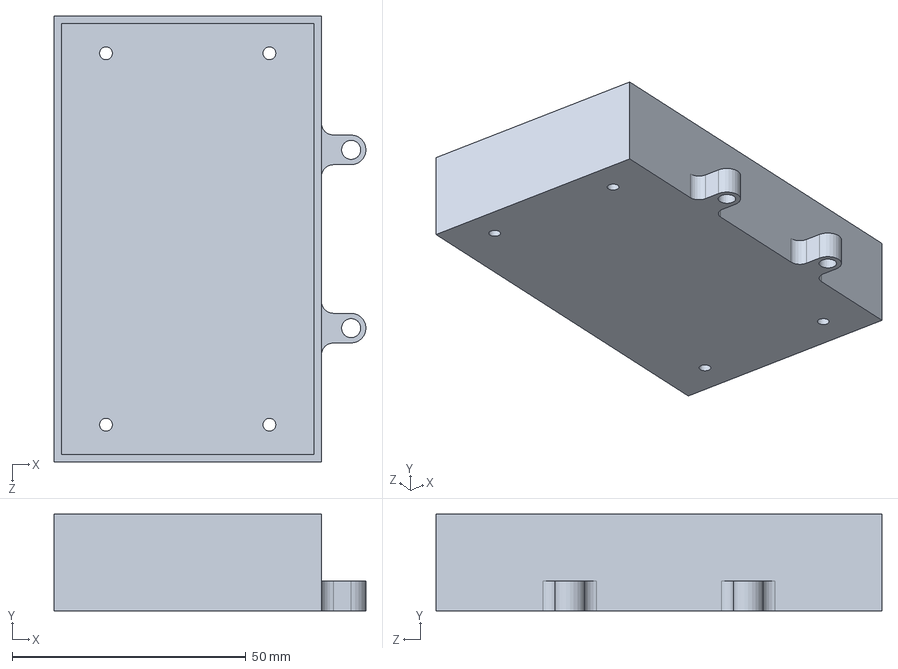
[picture p53: CAD file, 2025-11-15]
Mechanical/Experimental/Swerve Modules/UWBMount.SLDPRT
66.7 x 20.6 x 95.2 mm
