Matthew0826/NULunabotics/Mechanical/Experimental/Swerve Modules/Wheel Structure/12mm Coupler.STEP

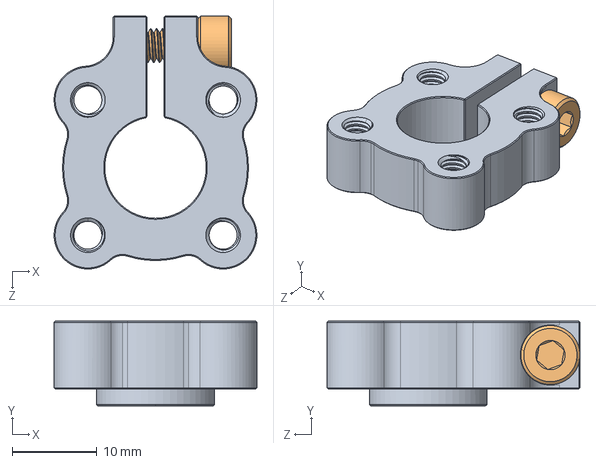
[picture p54: CAD file, 2024-11-07]
Mechanical/Experimental/Swerve Modules/Wheel Structure/12mm Coupler.STEP
24.0 x 10.0 x 29.9 mm
2800-0004-0010_90128A207
