Matthew0826/NULunabotics/Mechanical/Experimental/Swerve Modules/Wheel Structure/Fixed Components/Wheel Cover Plate.SLDPRT

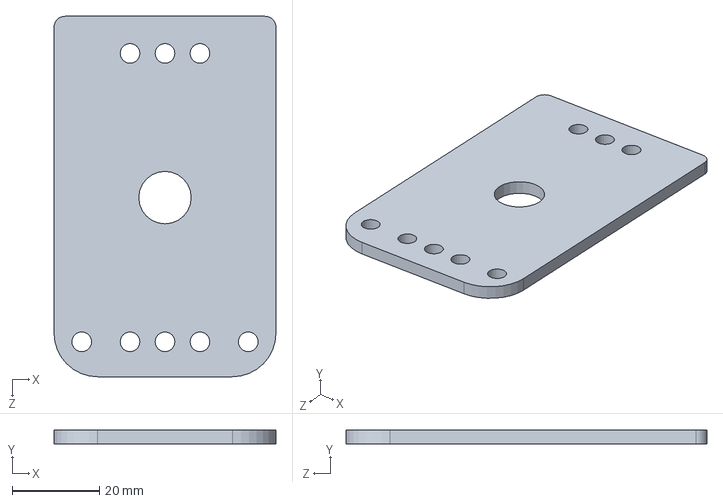
[picture p55: CAD file, 2025-11-15]
Mechanical/Experimental/Swerve Modules/Wheel Structure/Fixed Components/Wheel Cover Plate.SLDPRT
50.8 x 3.17 x 82.5 mm
