Matthew0826/NULunabotics/Mechanical/Lunabotics2025_Chassis_Design/CAD_Lunbotics 2025/Chassis Frame.SLDPRT

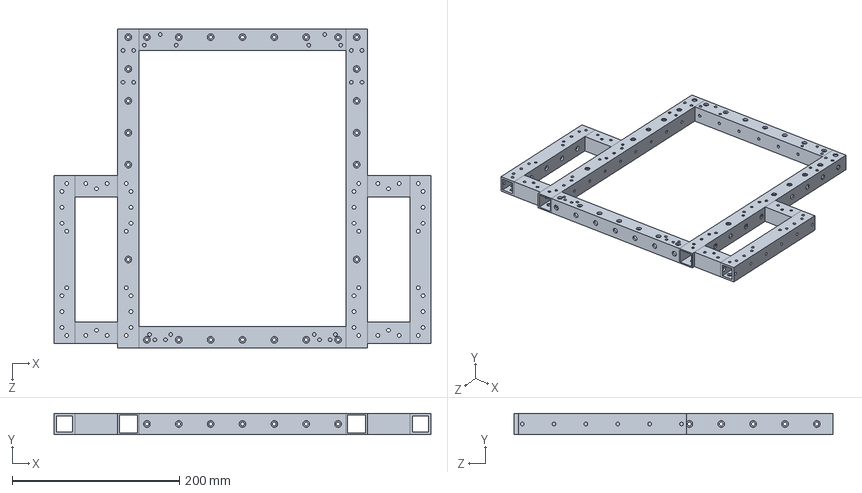
[picture p56: CAD file, 2025-03-20]
Mechanical/Lunabotics2025_Chassis_Design/CAD_Lunbotics 2025/Chassis Frame.SLDPRT
450.9 x 25.4 x 381.0 mm
