Matthew0826/NULunabotics/Mechanical/Lunabotics2025_Chassis_Design/Chassis_3/9x6inch_side_frame_dxf.DXF

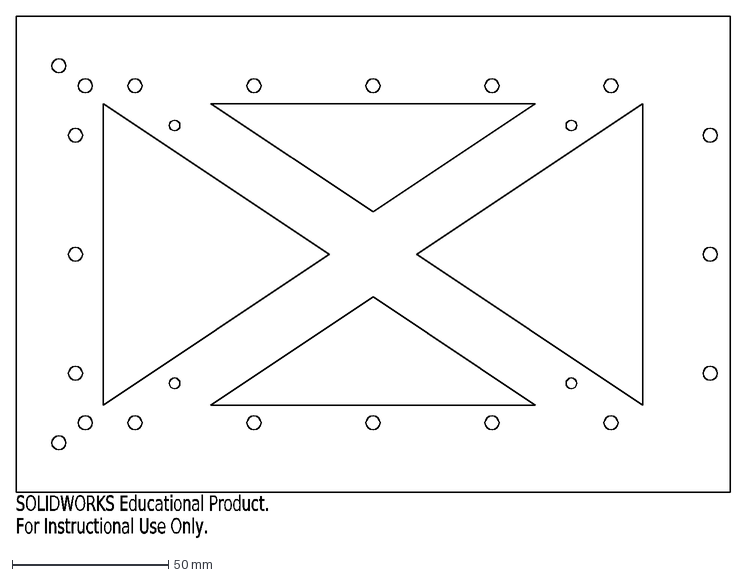
[picture p58: CAD file, 2025-03-20]
Mechanical/Lunabotics2025_Chassis_Design/Chassis_3/9x6inch_side_frame_dxf.DXF
SOLIDWORKS Educational Product.
For Instructional Use Only.
