Matthew0826/NULunabotics/Mechanical/Lunabotics2025_Chassis_Design/Conveyer/300MM_PVC.SLDPRT

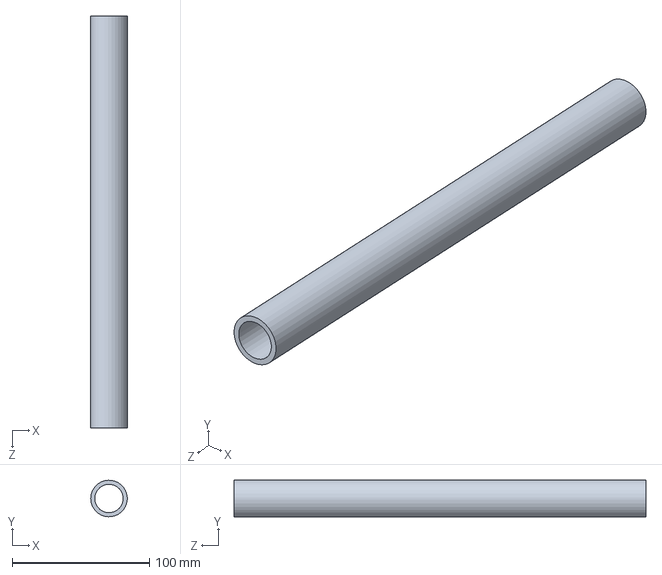
[picture p59: CAD file, 2025-02-18]
Mechanical/Lunabotics2025_Chassis_Design/Conveyer/300MM_PVC.SLDPRT
26.7 x 26.6 x 300.0 mm
