Matthew0826/NULunabotics/Mechanical/Lunabotics2025_Chassis_Design/Schematics_Bot.SLDPRT

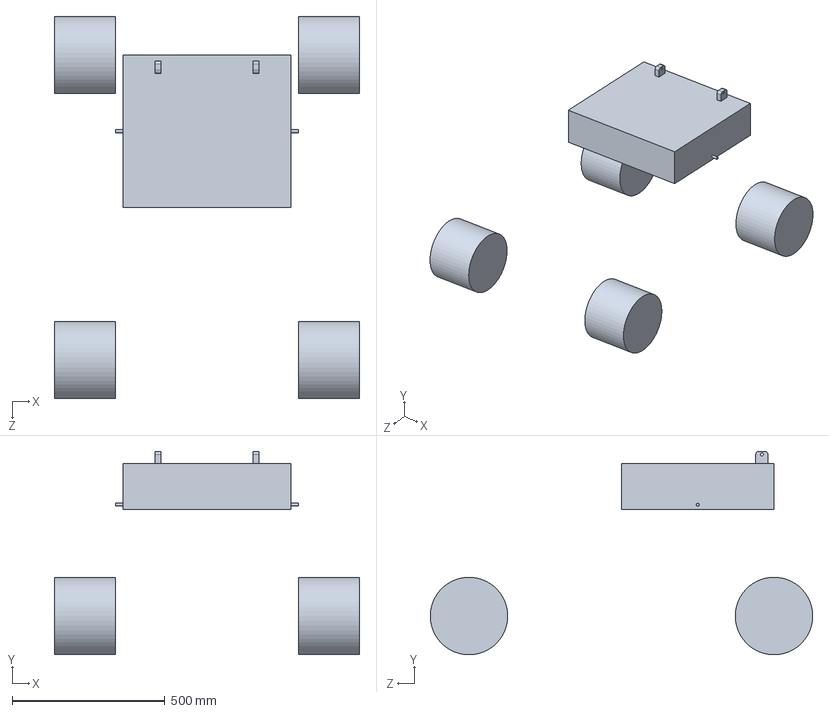
[picture p60: CAD file, 2025-02-18]
Mechanical/Lunabotics2025_Chassis_Design/Schematics_Bot.SLDPRT
1000.0 x 666.7 x 1254.0 mm
