Matthew0826/NULunabotics/Mechanical/OuterSPacer.SLDPRT

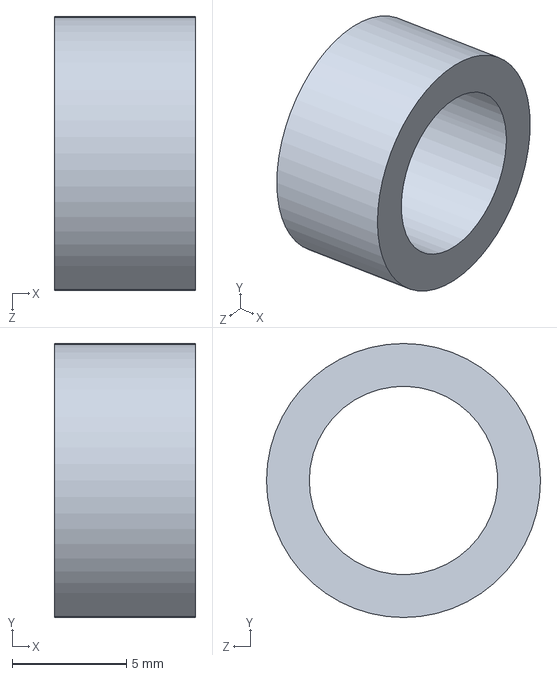
[picture p61: CAD file, 2025-11-15]
Mechanical/OuterSPacer.SLDPRT
6.18 x 12.0 x 12.0 mm
