Matthew0826/NULunabotics/Mechanical/Rocker/InnerSpacer4Bar.STL

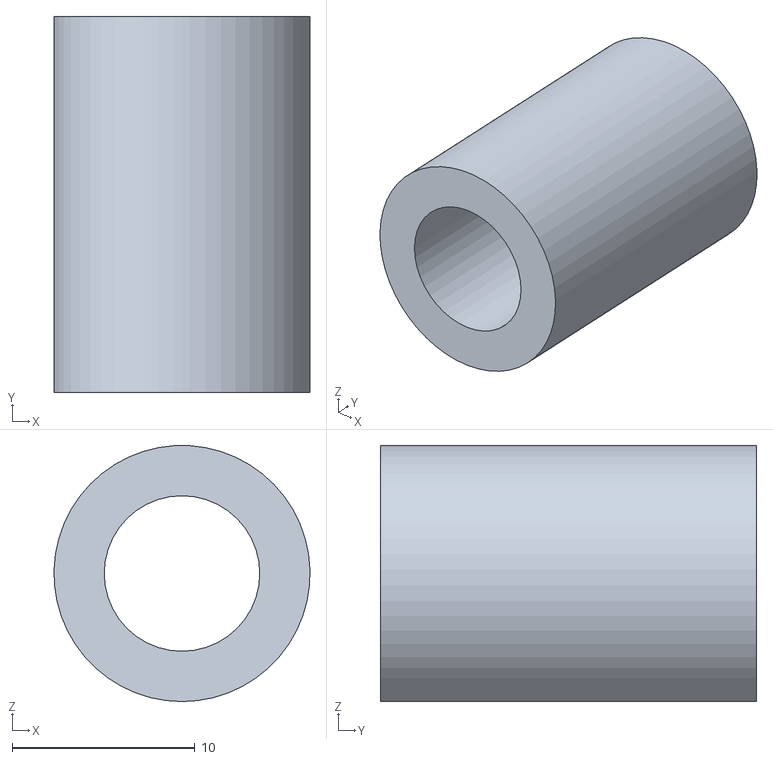
[picture p62: CAD file, 2025-11-15]
Mechanical/Rocker/InnerSpacer4Bar.STL
14.0 x 20.6 x 14.0
