Matthew0826/NULunabotics/Mechanical/Wheel/wheel_design_2.SLDPRT

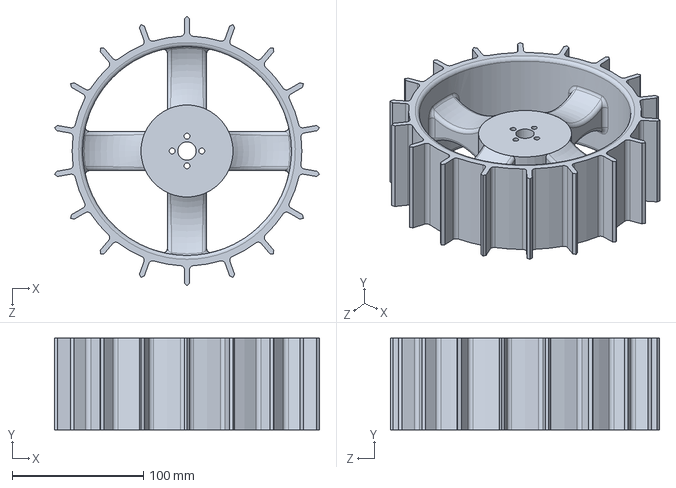
[picture p63: CAD file, 2025-03-14]
Mechanical/Wheel/wheel_design_2.SLDPRT
201.8 x 70.0 x 205.0 mm
