Matthew0826/NULunabotics/Software/ROS2/src/website/public/models/lunabot_excavator.obj

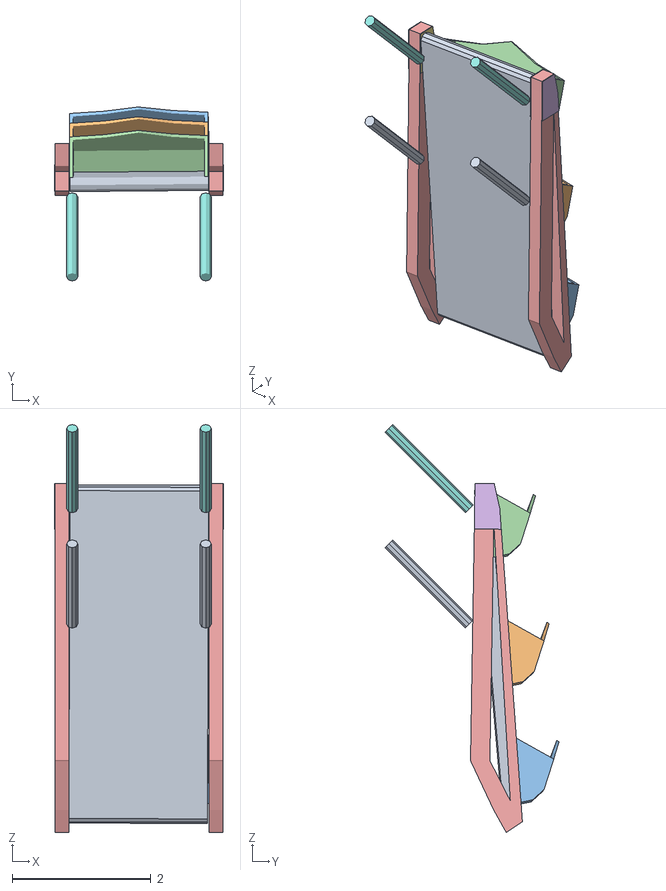
[picture p64: CAD file, 2025-11-15]
Software/ROS2/src/website/public/models/lunabot_excavator.obj
2.45 x 2.51 x 5.89
