Matthew0826/NULunabotics/Software/ROS2/src/website/public/models/theia/chasis.obj

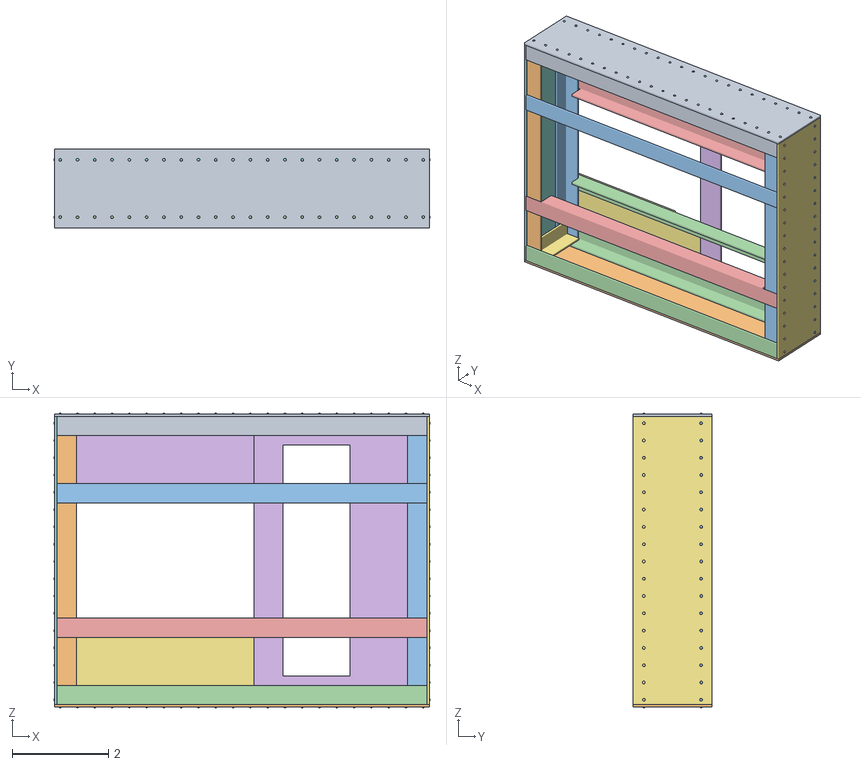
[picture p65: CAD file, 2025-11-15]
Software/ROS2/src/website/public/models/theia/chasis.obj
7.83 x 1.65 x 6.13
Truss
Truss.001
Truss.002
Truss.003
Truss.004
Truss.005
Truss.006
Truss.007
Truss.008
Truss.009
Truss.010
Truss.011
Truss.014
Truss.013
Truss.015
Truss.016
Truss.017
Truss.018
Truss.022
Screw
Screw.001
Screw.002
Screw.003
Screw.004
Screw.005
Screw.006
Screw.007
Truss.019
Truss.012
Truss.027
Truss.028
