Matthew0826/NULunabotics/Mechanical/Chassis/Chassis v4/Slotted Box L-Bar.SLDPRT

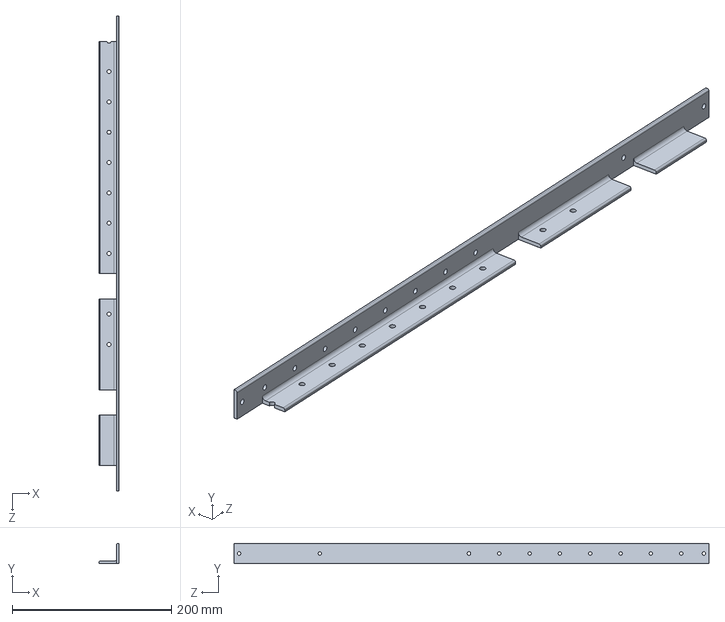
[picture p66: CAD file, 2025-11-15]
Mechanical/Chassis/Chassis v4/Slotted Box L-Bar.SLDPRT
25.4 x 25.4 x 596.9 mm
