Matthew0826/NULunabotics/Mechanical/Chassis/Sheet Metal Chassis/Chassis_Bottom-Shell.SLDPRT

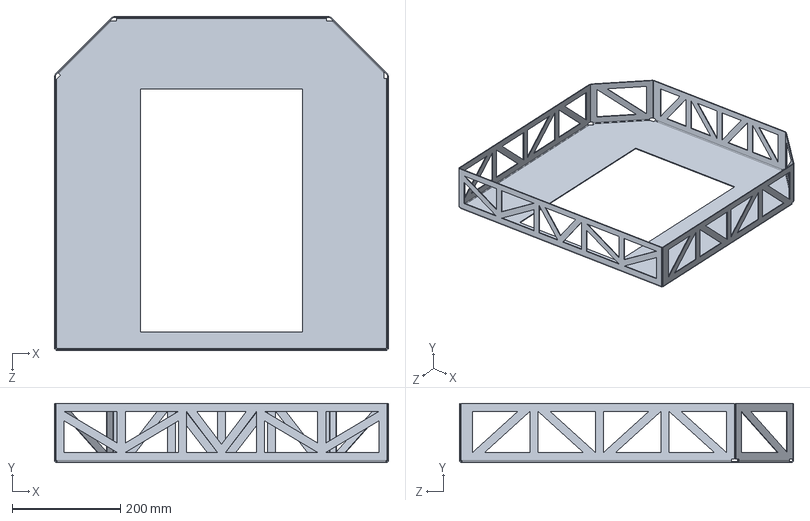
[picture p67: CAD file, 2025-02-20]
Mechanical/Chassis/Sheet Metal Chassis/Chassis_Bottom-Shell.SLDPRT
618.0 x 110.0 x 618.0 mm
