Matthew0826/NULunabotics/Mechanical/Excavation/BearingStandin14.STL

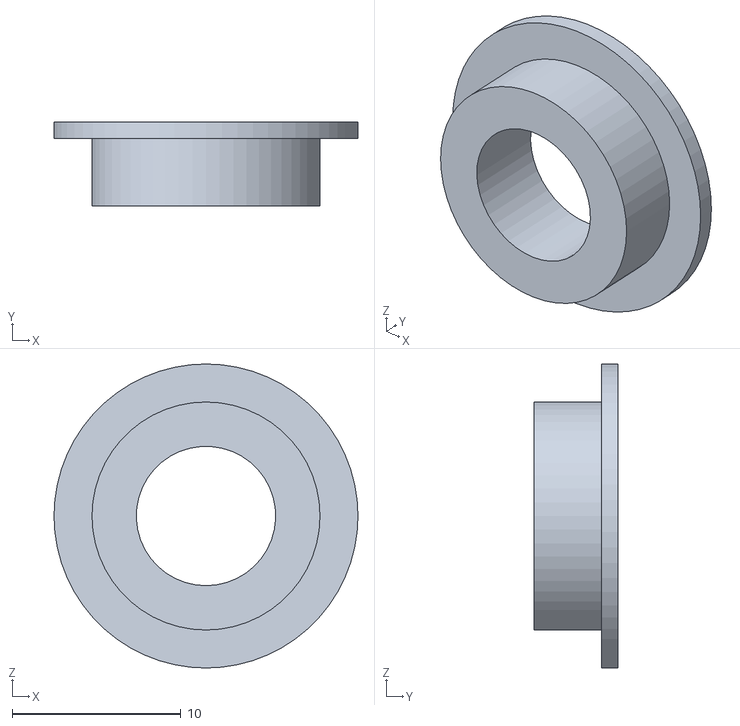
[picture p68: CAD file, 2025-11-15]
Mechanical/Excavation/BearingStandin14.STL
18.0 x 5.00 x 18.0
