Matthew0826/NULunabotics/Mechanical/Excavation/Excavator/plat.DXF

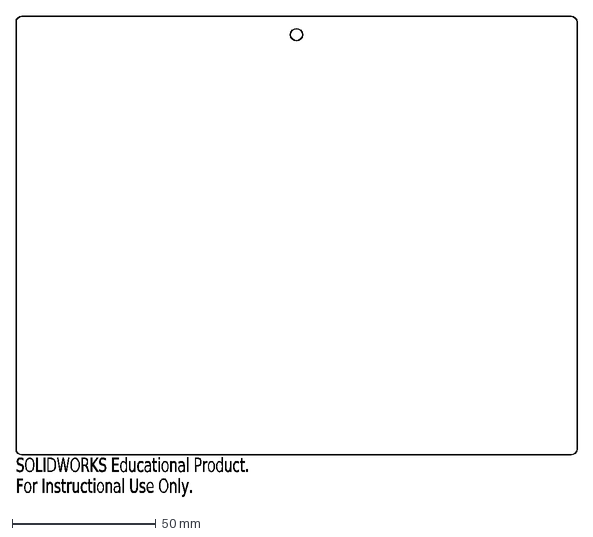
[picture p69: CAD file, 2025-11-15]
Mechanical/Excavation/Excavator/plat.DXF
SOLIDWORKS Educational Product.
For Instructional Use Only.
