Matthew0826/NULunabotics/Mechanical/Experimental/Swerve Modules/Chassis Structure/32mm D-shaft.SLDPRT

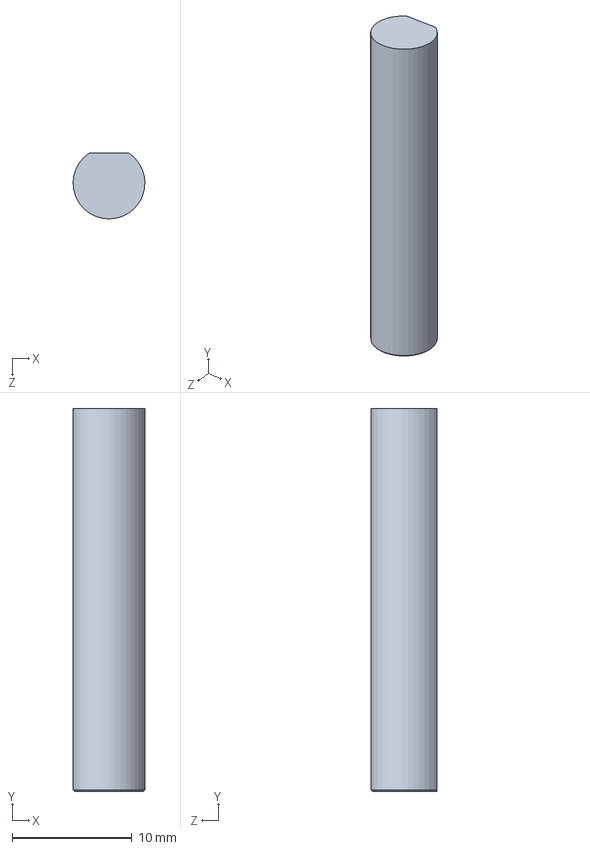
[picture p70: CAD file, 2025-02-19]
Mechanical/Experimental/Swerve Modules/Chassis Structure/32mm D-shaft.SLDPRT
6.00 x 32.0 x 5.50 mm
