Matthew0826/NULunabotics/Mechanical/Experimental/Swerve Modules/Chassis Structure/Fixed Components/Gearbox Casing/Lamprey.SLDPRT

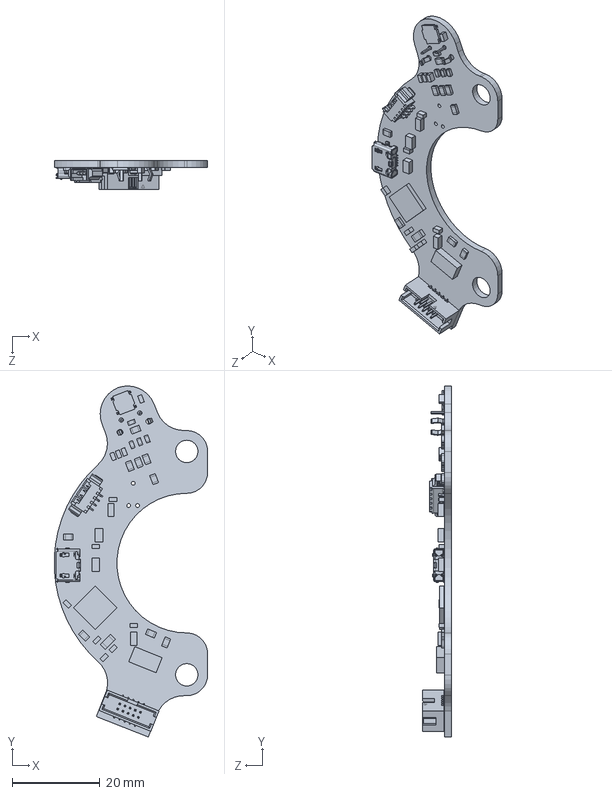
[picture p71: CAD file, 2025-02-19]
Mechanical/Experimental/Swerve Modules/Chassis Structure/Fixed Components/Gearbox Casing/Lamprey.SLDPRT
34.9 x 79.8 x 6.65 mm
