Matthew0826/NULunabotics/Mechanical/Experimental/Swerve Modules/Wheel Structure/28 Tooth Bevel Gear.STEP

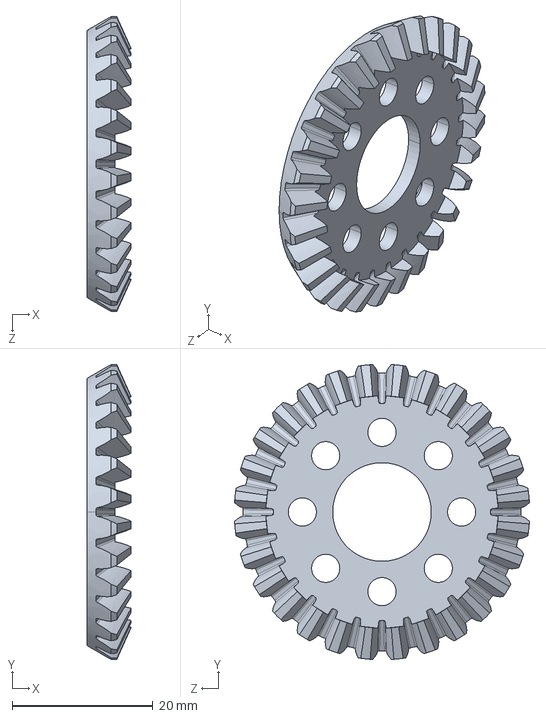
[picture p72: CAD file, 2024-11-07]
Mechanical/Experimental/Swerve Modules/Wheel Structure/28 Tooth Bevel Gear.STEP
6.28 x 41.9 x 41.9 mm
