Matthew0826/NULunabotics/Mechanical/Experimental/Swerve Modules/Wheel Structure/Fixed Components/Bottom Interface Plate.STEP

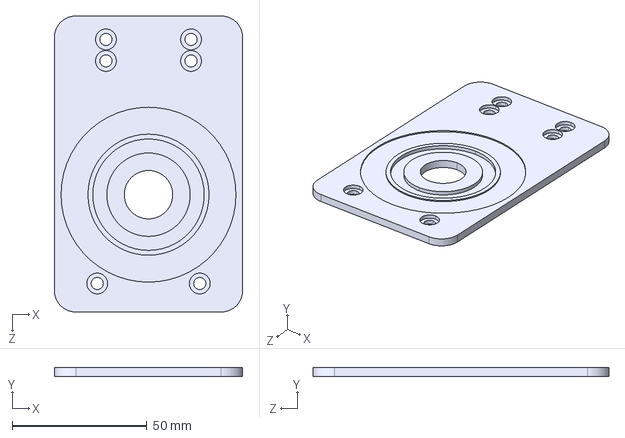
[picture p73: CAD file, 2025-03-20]
Mechanical/Experimental/Swerve Modules/Wheel Structure/Fixed Components/Bottom Interface Plate.STEP
70.0 x 3.17 x 110.0 mm
