Matthew0826/NULunabotics/Mechanical/Lunabotics2025_Chassis_Design/CAD_Lunbotics 2025/square_Frame_gusset_2.SLDPRT

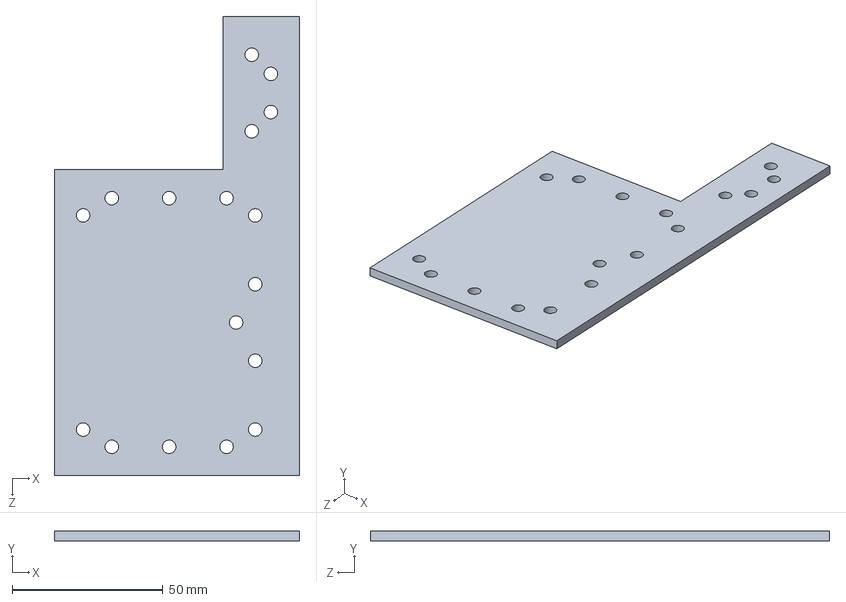
[picture p74: CAD file, 2025-03-20]
Mechanical/Lunabotics2025_Chassis_Design/CAD_Lunbotics 2025/square_Frame_gusset_2.SLDPRT
81.4 x 3.17 x 152.4 mm
