Matthew0826/NULunabotics/Mechanical/Lunabotics2025_Chassis_Design/Chassis_3/L-Bar_1x1_8th_inch_449.2mm.SLDPRT

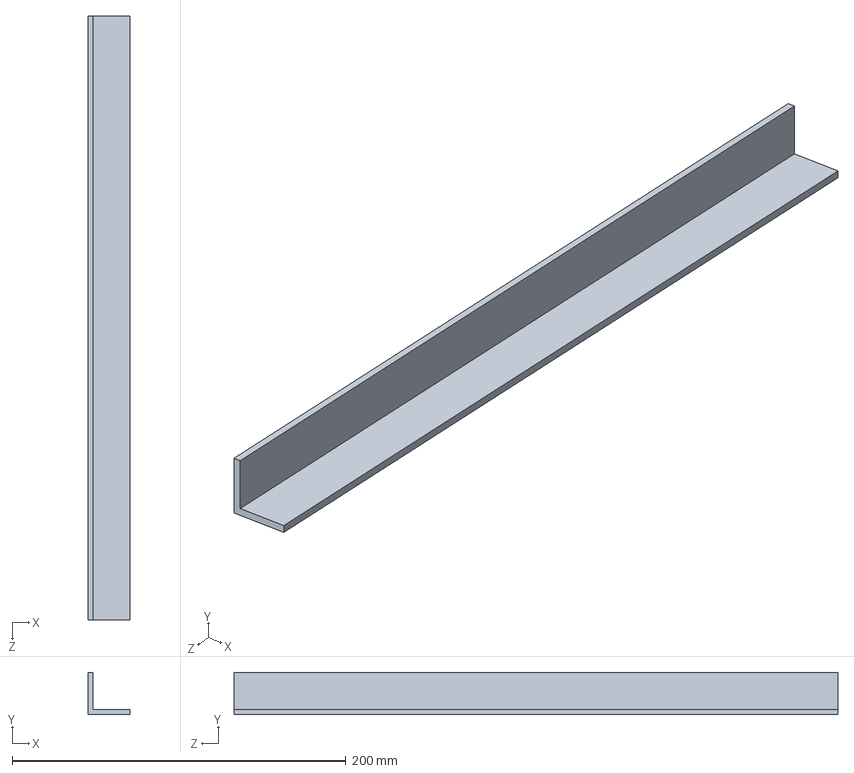
[picture p76: CAD file, 2025-03-20]
Mechanical/Lunabotics2025_Chassis_Design/Chassis_3/L-Bar_1x1_8th_inch_449.2mm.SLDPRT
25.4 x 25.4 x 362.0 mm
