Matthew0826/NULunabotics/Mechanical/Lunabotics2025_Chassis_Design/Conveyer/Rib_2.SLDPRT

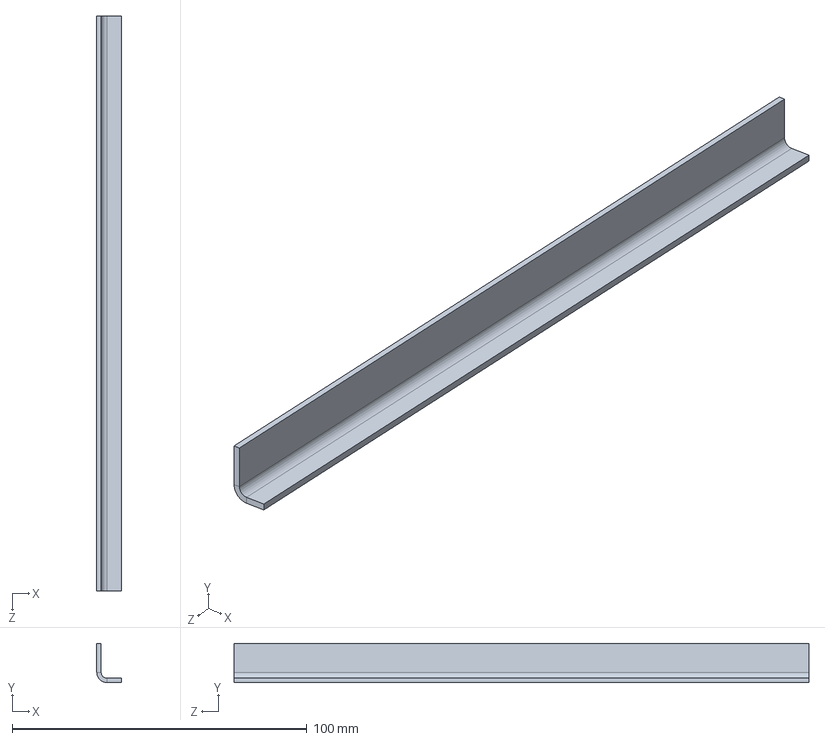
[picture p77: CAD file, 2025-02-18]
Mechanical/Lunabotics2025_Chassis_Design/Conveyer/Rib_2.SLDPRT
8.32 x 13.3 x 195.0 mm
