Matthew0826/NULunabotics/Mechanical/Lunabotics2025_Chassis_Design/Dummy_Hinge.SLDPRT

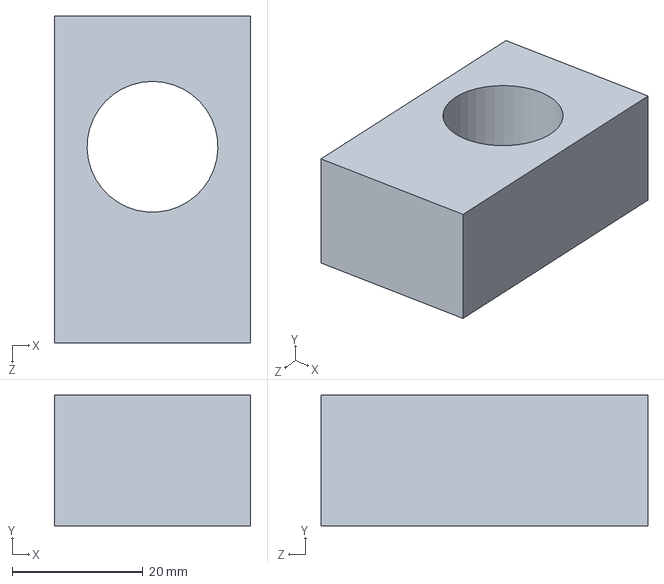
[picture p78: CAD file, 2025-02-18]
Mechanical/Lunabotics2025_Chassis_Design/Dummy_Hinge.SLDPRT
30.0 x 20.0 x 50.0 mm
