Matthew0826/NULunabotics/Mechanical/MotorMointBtm.DXF

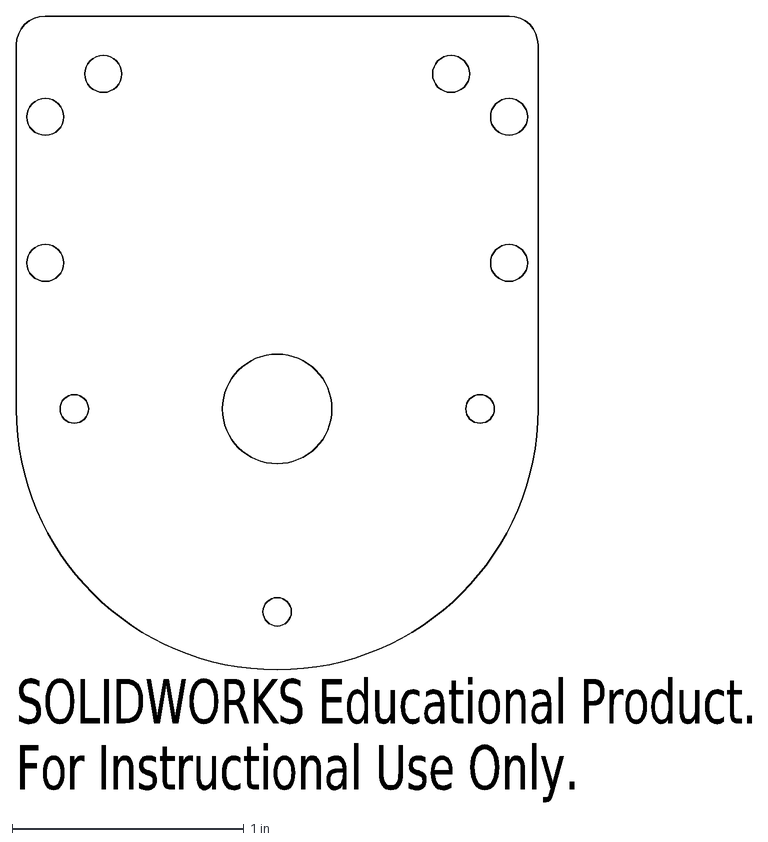
[picture p79: CAD file, 2025-11-15]
Mechanical/MotorMointBtm.DXF
SOLIDWORKS Educational Product.
For Instructional Use Only.
