Matthew0826/NULunabotics/Mechanical/Rocker/Motor Direct Holder_imported_ai.dxf

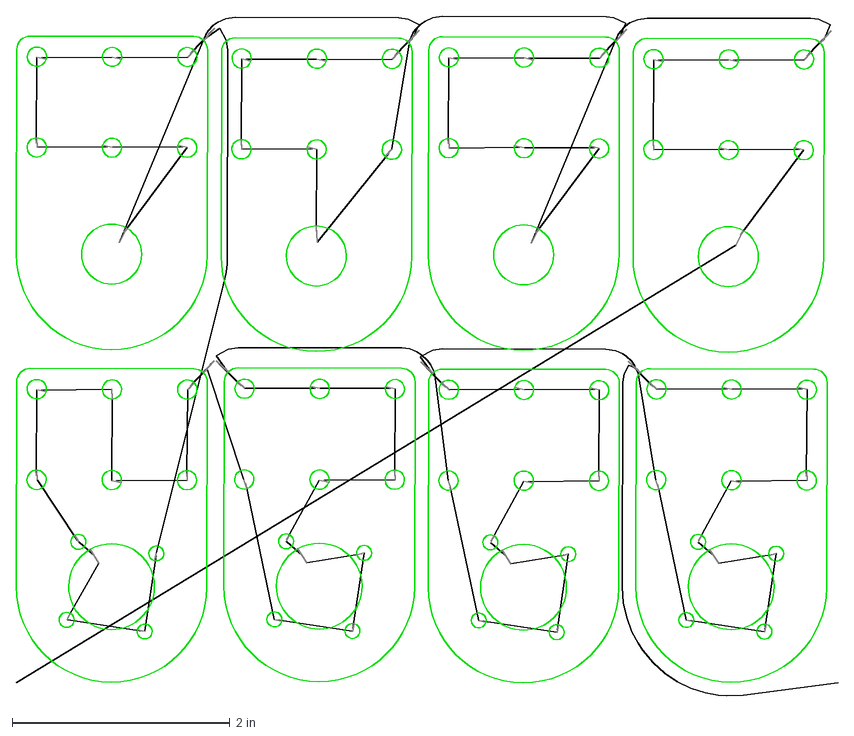
[picture p80: CAD file, 2025-11-15]
Mechanical/Rocker/Motor Direct Holder_imported_ai.dxf
7.54 x 6.23 in
