Matthew0826/NULunabotics/Software/ROS2/src/website/public/models/lunabot4.obj

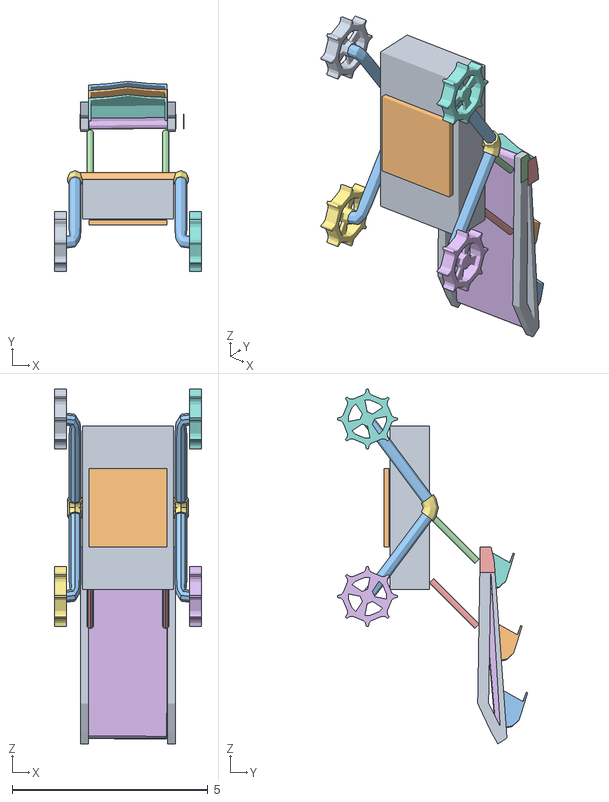
[picture p81: CAD file, 2025-11-15]
Software/ROS2/src/website/public/models/lunabot4.obj
3.76 x 4.86 x 9.07
Wheel.001
Wheel.002
Wheel.003
Wheel.004
Bin
