Matthew0826/NULunabotics/Mechanical/;;.dxf

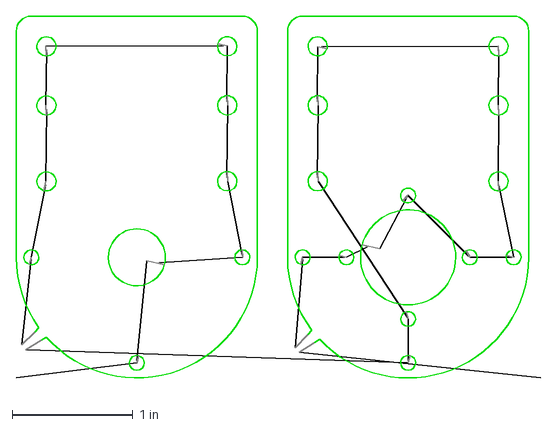
[picture p82: CAD file, 2025-11-15]
Mechanical/;;.dxf
4.35 x 3.08 in
