Matthew0826/NULunabotics/Mechanical/Chassis/Chassis v4/LargeTopPlate.SLDPRT

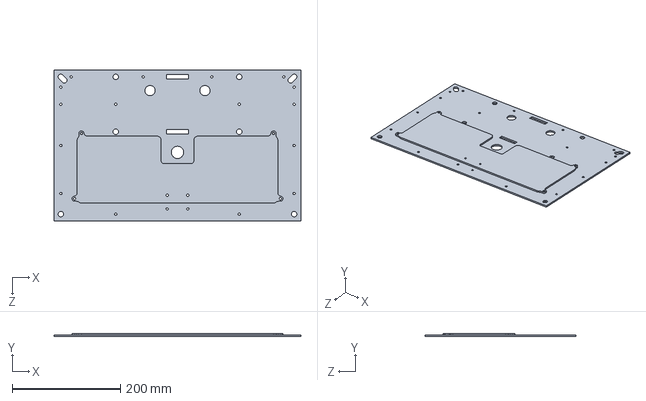
[picture p83: CAD file, 2025-11-15]
Mechanical/Chassis/Chassis v4/LargeTopPlate.SLDPRT
457.2 x 6.35 x 279.4 mm
