Matthew0826/NULunabotics/Mechanical/Chassis/Sheet Metal Chassis/Chassis Frame.SLDPRT

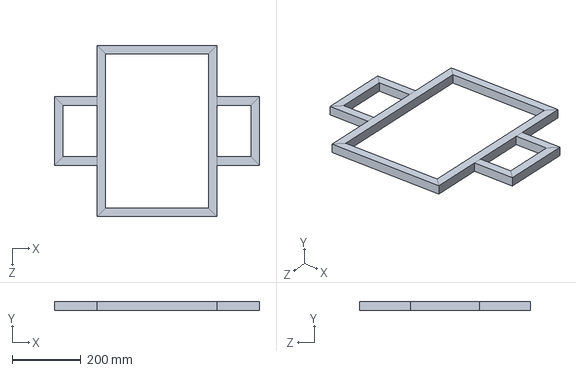
[picture p84: CAD file, 2025-02-20]
Mechanical/Chassis/Sheet Metal Chassis/Chassis Frame.SLDPRT
598.0 x 25.0 x 500.0 mm
