Matthew0826/NULunabotics/Mechanical/Excavation/Dump/DumpCut_imported_ai.dxf

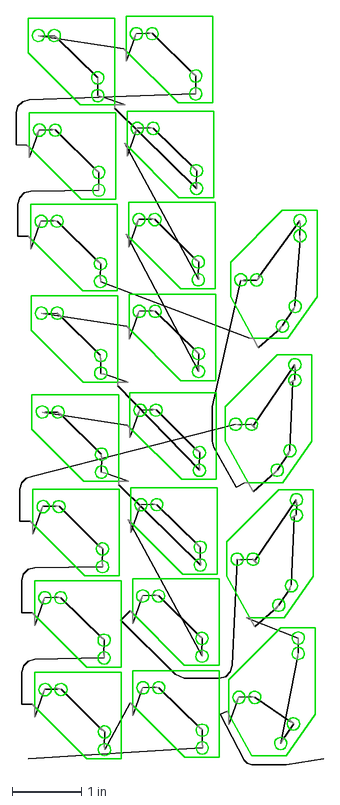
[picture p85: CAD file, 2025-11-15]
Mechanical/Excavation/Dump/DumpCut_imported_ai.dxf
4.45 x 10.8 in
