Matthew0826/NULunabotics/Mechanical/Excavation/Hex Cap.SLDPRT

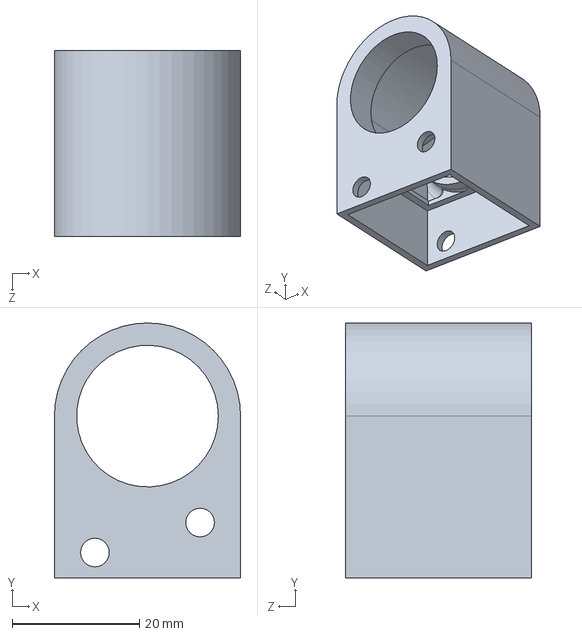
[picture p86: CAD file, 2025-11-15]
Mechanical/Excavation/Hex Cap.SLDPRT
29.2 x 40.0 x 29.2 mm
