Matthew0826/NULunabotics/Mechanical/Experimental/Swerve Modules/Chassis Structure/Fixed Components/Tube Mount/Tube.SLDPRT

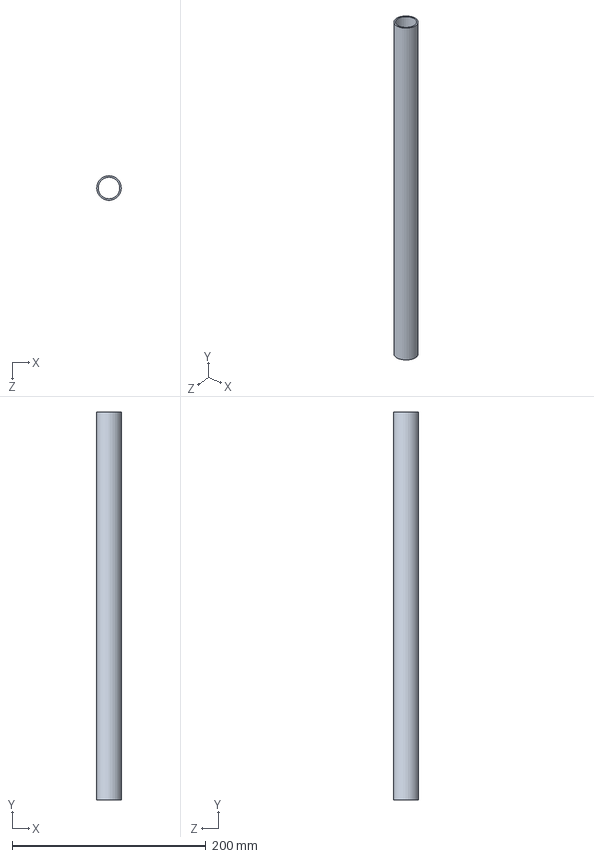
[picture p87: CAD file, 2025-02-19]
Mechanical/Experimental/Swerve Modules/Chassis Structure/Fixed Components/Tube Mount/Tube.SLDPRT
25.4 x 400.0 x 25.4 mm
