Matthew0826/NULunabotics/Mechanical/Experimental/Swerve Modules/Wheel Structure/Fixed Components/43mm Hex Standoff.STEP

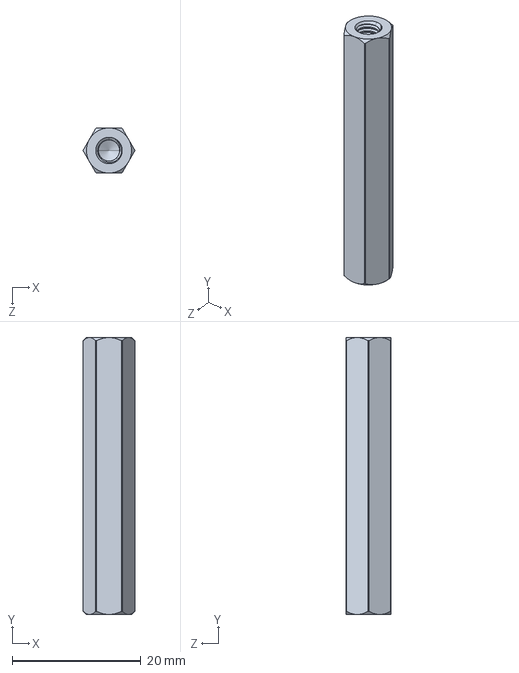
[picture p88: CAD file, 2025-02-19]
Mechanical/Experimental/Swerve Modules/Wheel Structure/Fixed Components/43mm Hex Standoff.STEP
8.00 x 43.0 x 7.00 mm
