Matthew0826/NULunabotics/Mechanical/Lunabotics2025_Chassis_Design/CAD_Lunbotics 2025/Box_corner_1.SLDPRT

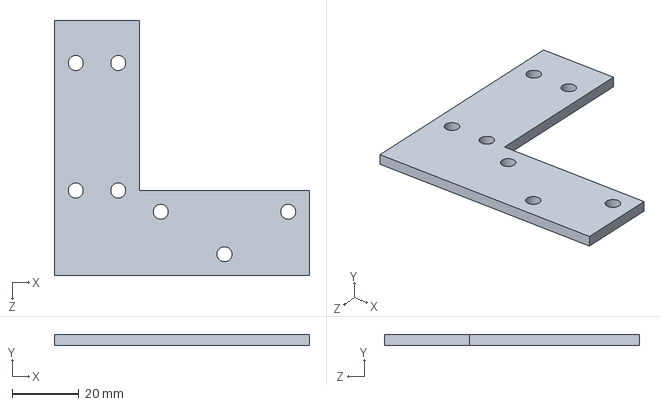
[picture p89: CAD file, 2025-03-20]
Mechanical/Lunabotics2025_Chassis_Design/CAD_Lunbotics 2025/Box_corner_1.SLDPRT
76.2 x 3.17 x 76.2 mm
