Matthew0826/NULunabotics/Mechanical/Rocker/OuterSpacer.STL

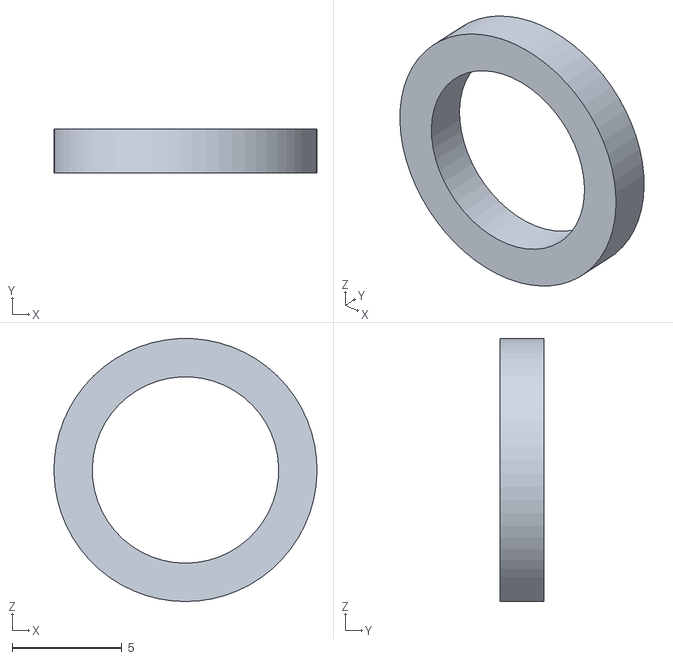
[picture p92: CAD file, 2025-11-15]
Mechanical/Rocker/OuterSpacer.STL
12.0 x 2.00 x 12.0
