Matthew0826/NULunabotics/Mechanical/4BarGBInnerLgr.STL

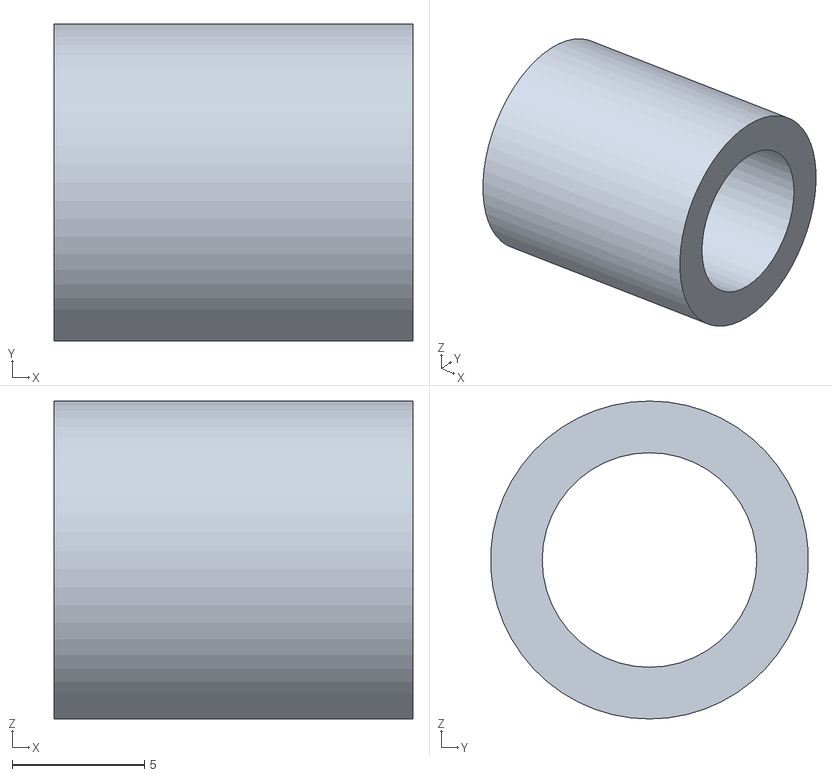
[picture p93: CAD file, 2025-11-15]
Mechanical/4BarGBInnerLgr.STL
13.5 x 12.0 x 12.0
