Matthew0826/NULunabotics/Mechanical/Chassis/Chassis v4/DoubleBearingHolder.SLDPRT

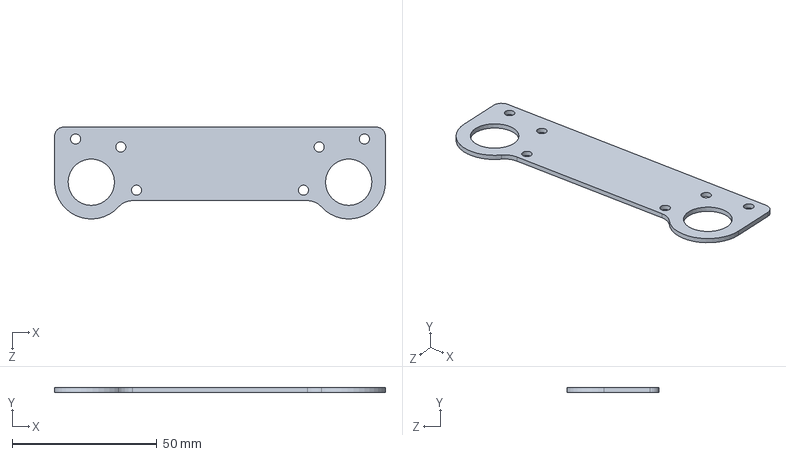
[picture p94: CAD file, 2025-11-15]
Mechanical/Chassis/Chassis v4/DoubleBearingHolder.SLDPRT
114.3 x 1.59 x 31.7 mm
