Matthew0826/NULunabotics/Mechanical/Chassis/Sheet Metal Chassis/296x110_Panel.SLDPRT

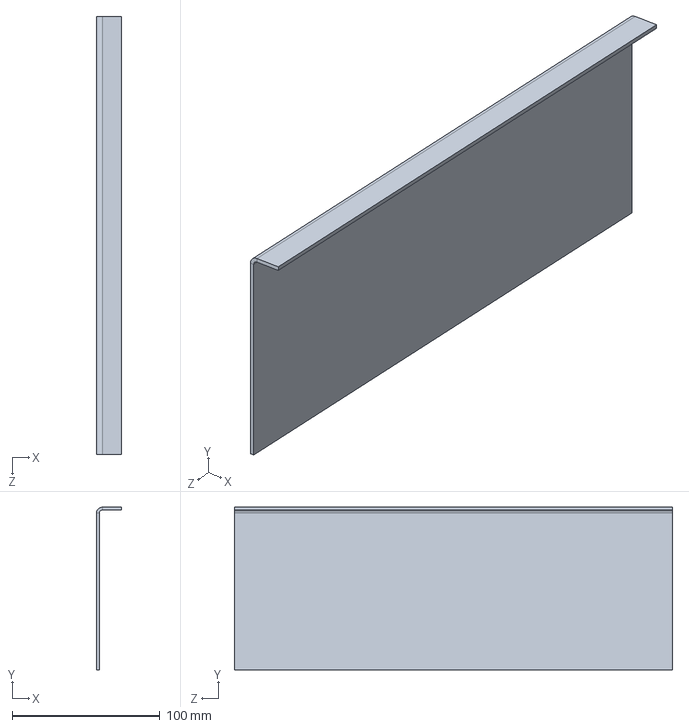
[picture p95: CAD file, 2025-02-20]
Mechanical/Chassis/Sheet Metal Chassis/296x110_Panel.SLDPRT
17.0 x 110.0 x 296.0 mm
