Matthew0826/NULunabotics/Mechanical/Excavation/Conveyer/PVC_Attachment2.SLDPRT

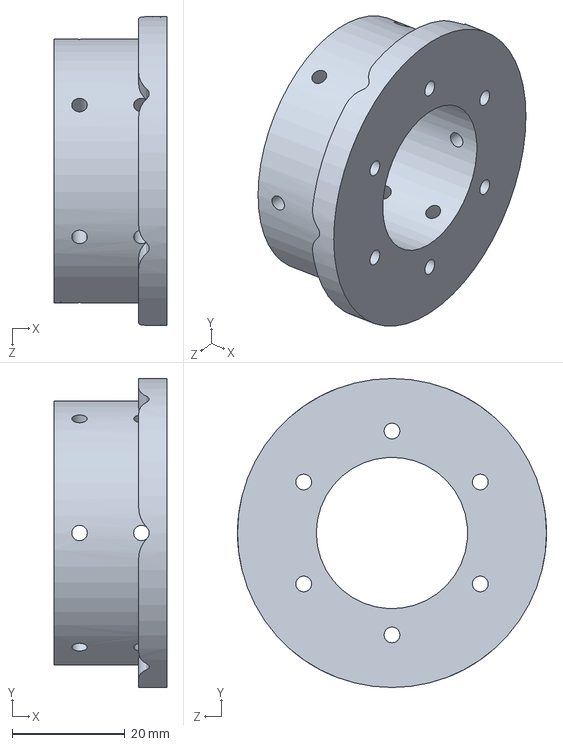
[picture p96: CAD file, 2025-02-20]
Mechanical/Excavation/Conveyer/PVC_Attachment2.SLDPRT
20.0 x 54.9 x 54.9 mm
