Matthew0826/NULunabotics/Mechanical/Excavation/Dump/DumpSide.SLDPRT

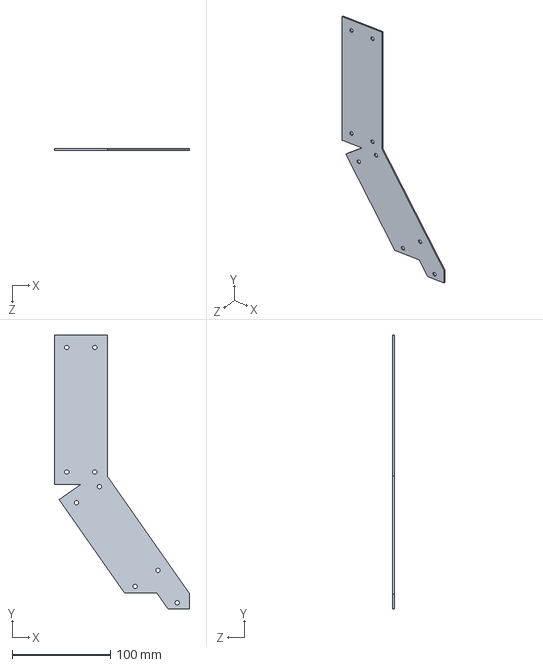
[picture p97: CAD file, 2025-11-15]
Mechanical/Excavation/Dump/DumpSide.SLDPRT
138.0 x 279.4 x 1.59 mm
