Matthew0826/NULunabotics/Mechanical/Excavation/Excavator/Knee Gusset1.STL

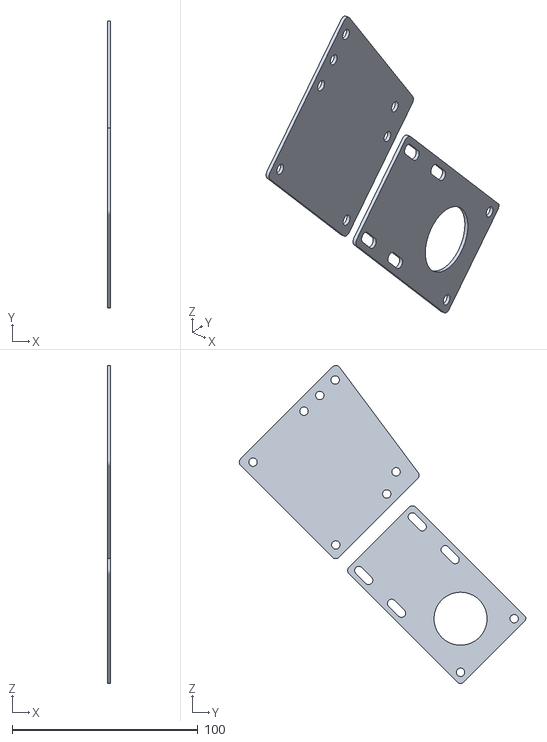
[picture p98: CAD file, 2025-11-15]
Mechanical/Excavation/Excavator/Knee Gusset1.STL
1.59 x 154.3 x 171.2
