Matthew0826/NULunabotics/Mechanical/Excavation/MountHolder.SLDPRT

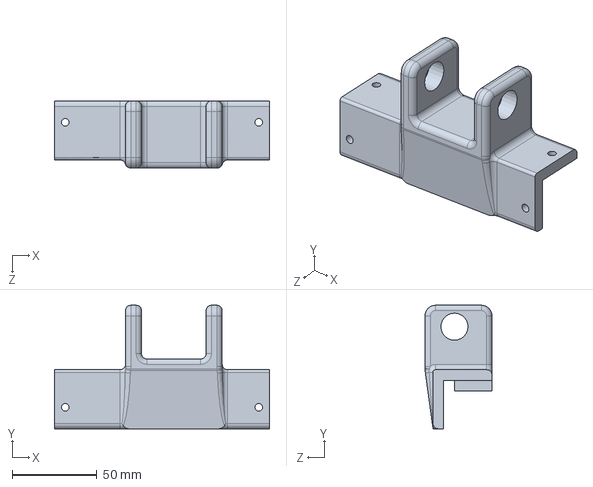
[picture p99: CAD file, 2025-11-15]
Mechanical/Excavation/MountHolder.SLDPRT
127.0 x 73.0 x 39.7 mm
