Matthew0826/NULunabotics/Mechanical/Lunabotics2025_Chassis_Design/Chassis_2/Chassis_2_Assy.SLDASM

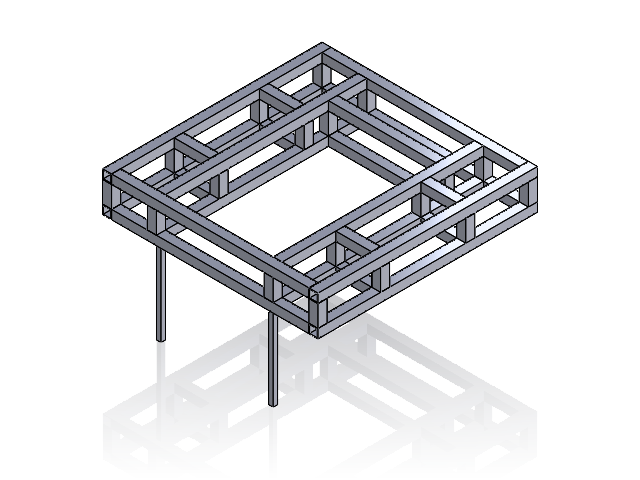
[picture p114: CAD file, 2025-02-27]
Mechanical/Lunabotics2025_Chassis_Design/Chassis_2/Chassis_2_Assy.SLDASM
1x1inch_612mmBeam x 4
1x1inch_550mmBeam x 4
1x1inch_561.2mmBeam x 4
1x1inch_300mmBeam x 2
1x1inch_60mmBeam x 18
1x1inch_99.6mmBeam x 8
0.5x0.5inch_240mmBeam x 2
