Matthew0826/NULunabotics/Mechanical/Chassis/Chassis v4/Chassis Assembly.SLDASM

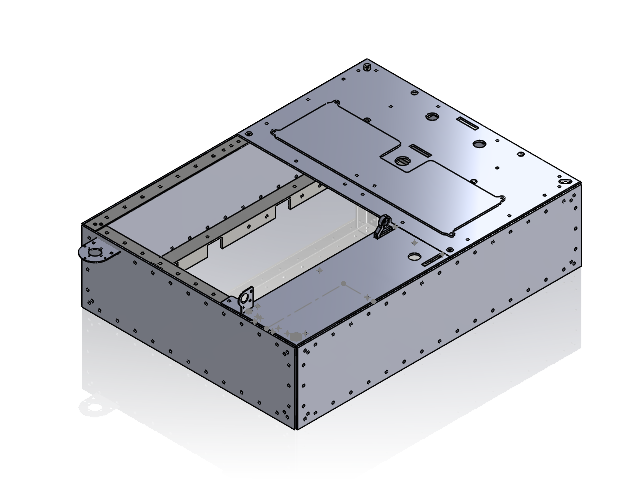
[picture p115: CAD file, 2025-11-15]
Mechanical/Chassis/Chassis v4/Chassis Assembly.SLDASM
Long-Side Horizontal L-Bar x 2
Short-Side Horizontal L-Bar x 4
Nut Holder x 3
Vertical L-Bar x 4
Slotted Box L-Bar x 2
LargeTopPlate
Side Plate x 2
Front Plate x 2
Small Top Plate
Part1^Chassis Assembly
1602-0032-0000.STEP
1611-0514-0008.STEP
Bearing Holder Standard
MotorMoint
