Matthew0826/NULunabotics/Mechanical/Excavation/Conveyer/Side_Frame_2_assy.SLDASM

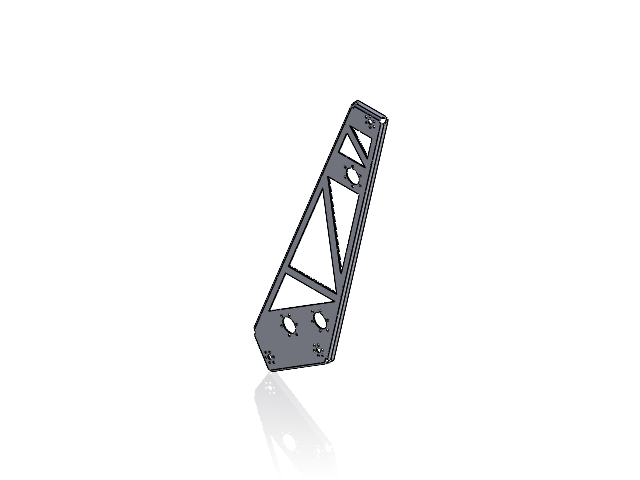
[picture p116: CAD file, 2025-02-20]
Mechanical/Excavation/Conveyer/Side_Frame_2_assy.SLDASM
Side_Frame_2
Rib_1
Rib_2
Rib_3
