Matthew0826/NULunabotics/Mechanical/Chassis/Chassis v4/Horizontal Assembly.SLDASM

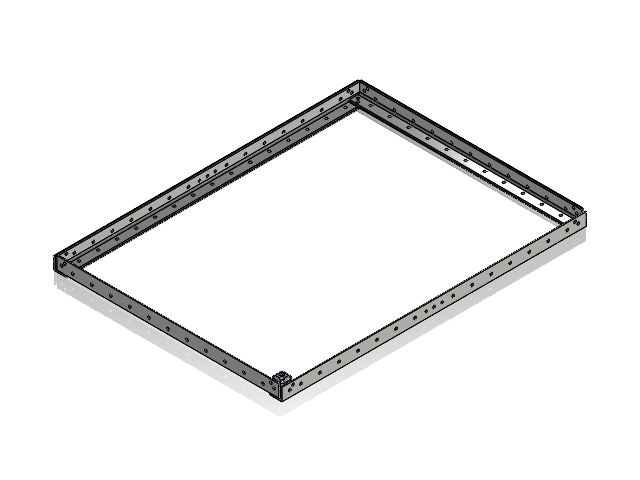
[picture p117: CAD file, 2025-11-15]
Mechanical/Chassis/Chassis v4/Horizontal Assembly.SLDASM
Long-Side Horizontal L-Bar x 2
Short-Side Horizontal L-Bar x 2
Nut Holder
