Matthew0826/NULunabotics/Mechanical/Excavation/Excavator/Assem1.SLDASM

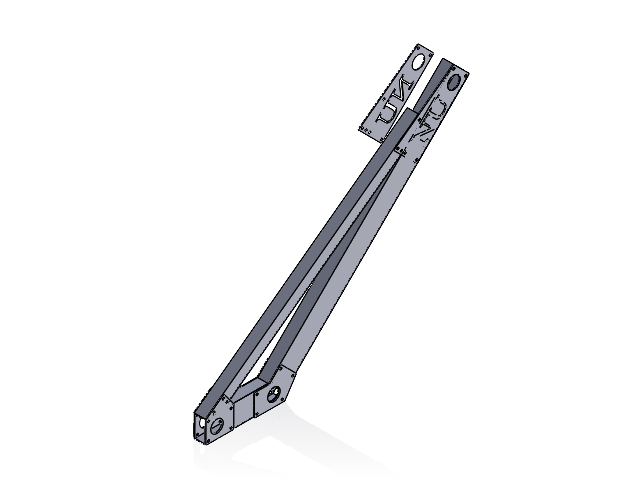
[picture p118: CAD file, 2025-11-15]
Mechanical/Excavation/Excavator/Assem1.SLDASM
Knee Gusset
Toe Gusset x 2
Tibia Tube
Foot Tube
Heel Gusset x 2
Mirrored Knee Gusset
Fibula Tube
