Matthew0826/NULunabotics/Mechanical/Rocker/Female Steel Ball Linkage.SLDASM

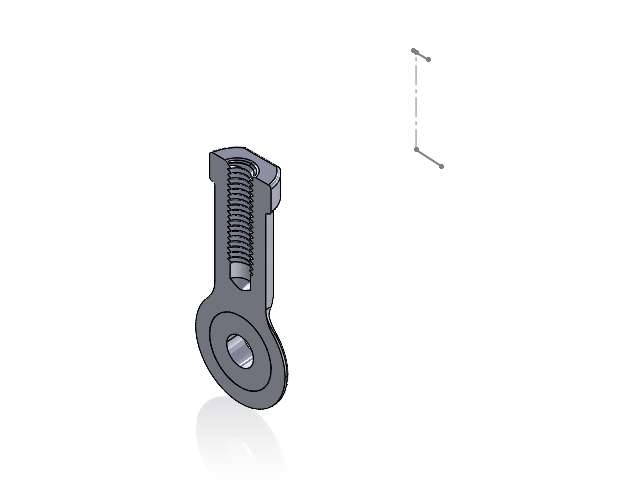
[picture p119: CAD file, 2025-02-24]
Mechanical/Rocker/Female Steel Ball Linkage.SLDASM
2913-0004-0241 housing.STEP
2913-0004-0241 ball.STEP
