Matthew0826/NULunabotics/Mechanical/Chassis/Chassis v4/Frame Chassis.SLDASM

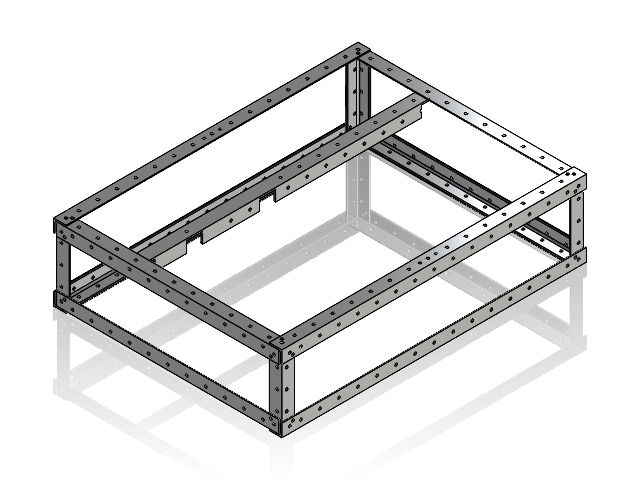
[picture p120: CAD file, 2025-11-15]
Mechanical/Chassis/Chassis v4/Frame Chassis.SLDASM
Long-Side Horizontal L-Bar x 4
Short-Side Horizontal L-Bar x 4
Nut Holder x 2
Vertical L-Bar x 4
Slotted Box L-Bar
