Matthew0826/NULunabotics/Mechanical/Excavation/Excavator/Excavator Assy.SLDASM

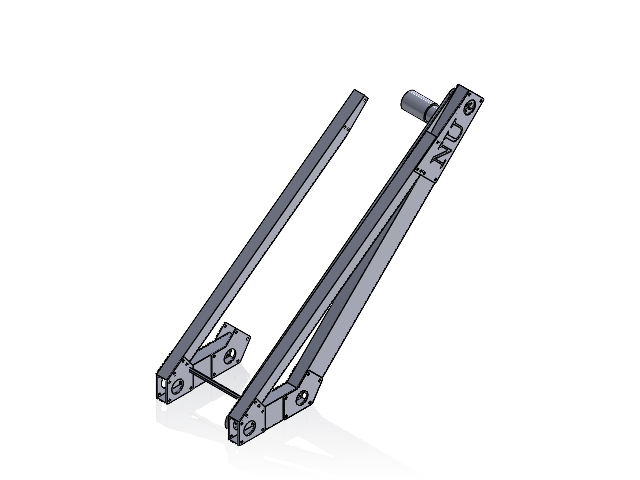
[picture p121: CAD file, 2025-03-20]
Mechanical/Excavation/Excavator/Excavator Assy.SLDASM
Heel Gusset x 5
Knee Gusset x 2
Toe Gusset x 4
Fibula Tube x 2
Tibia Tube x 2
Foot Tube x 2
am-4776 18T 25 Chain 375in Hex Symmetrical.step
Chain
StandOff
Motor
50 tooth gear.step
